jgratton72/Purple-38er/Images/Case 3D/CaseBase3D.jpg

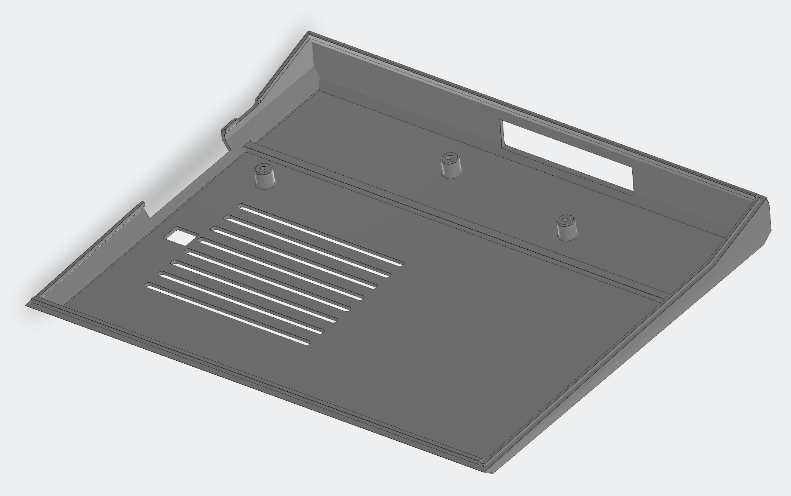
Images/Case 3D/CaseBase3D.jpg
