jgratton72/Purple-38er/Images/PCB 3D/Board3D.jpg

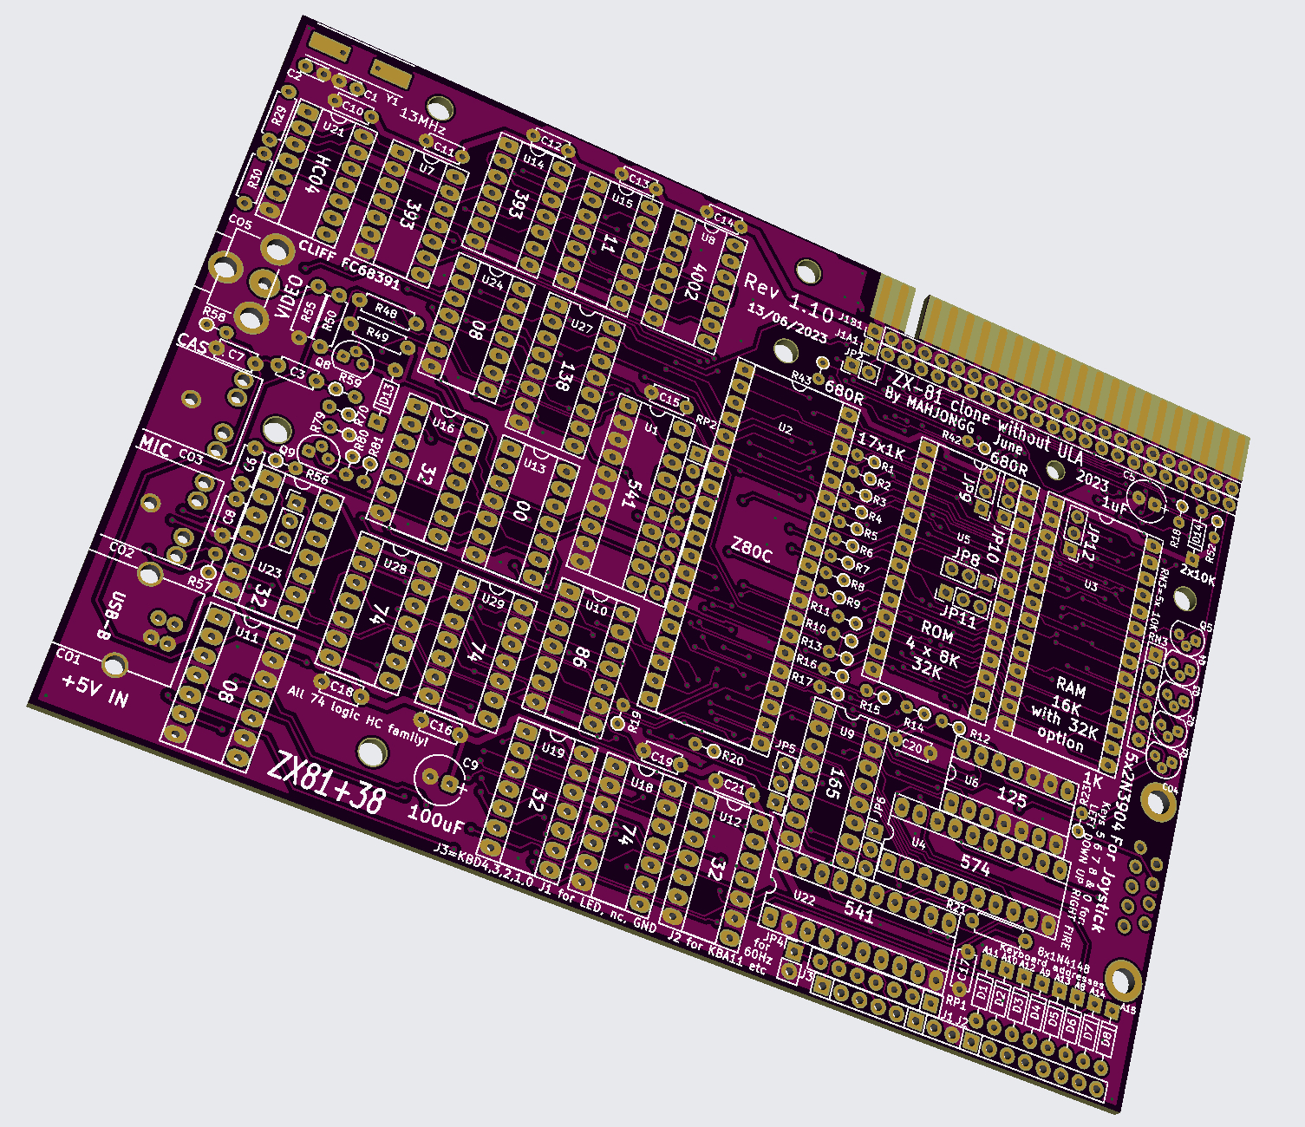
Images/PCB 3D/Board3D.jpg
