jgratton72/Purple-38er/Sources/Case/Case STEP/zx81-case-sinclair-5.step

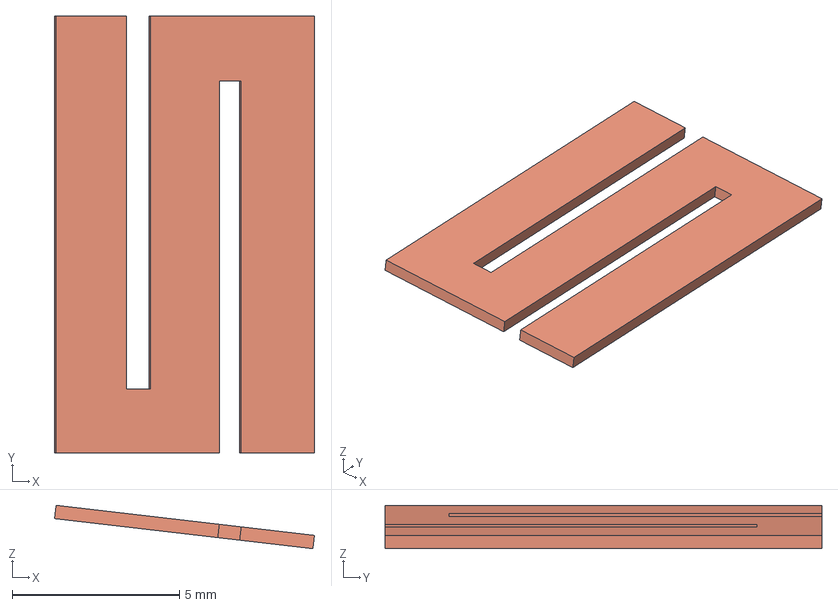
[picture p23: CAD file, 2025-08-02]
Sources/Case/Case STEP/zx81-case-sinclair-5.step
7.77 x 13.1 x 1.30 mm
