jgratton72/Purple-38er/Sources/Case/Keycap STEP/zx81-keycaps-text-b-39.step

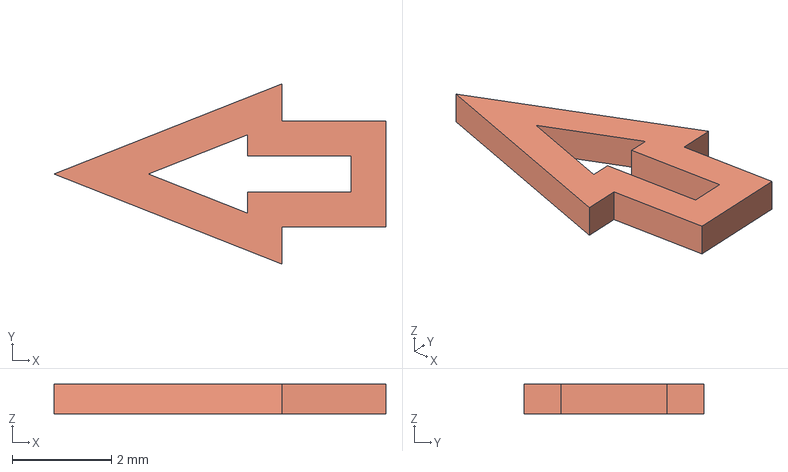
[picture p25: CAD file, 2025-08-02]
Sources/Case/Keycap STEP/zx81-keycaps-text-b-39.step
6.69 x 3.63 x 0.6 mm
