jgratton72/Purple-38er/Sources/Case/Case STEP/zx81-case-sinclair-1.step

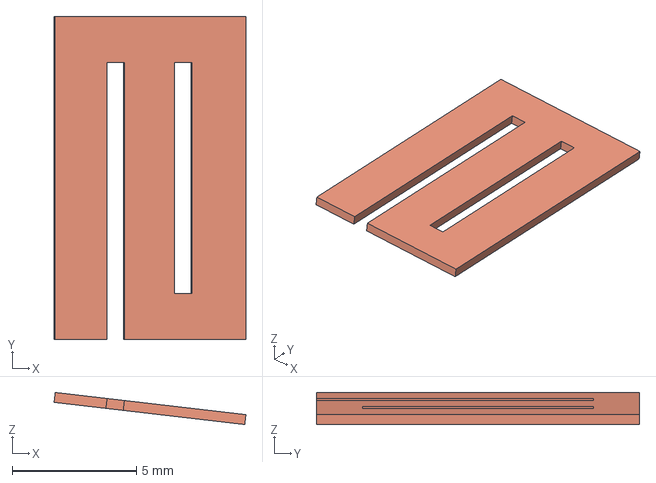
[picture p26: CAD file, 2025-08-02]
Sources/Case/Case STEP/zx81-case-sinclair-1.step
7.73 x 13.0 x 1.29 mm
