jgratton72/Purple-38er/Sources/Case/Keycap STEP/zx81-keycaps-text-b-32.step

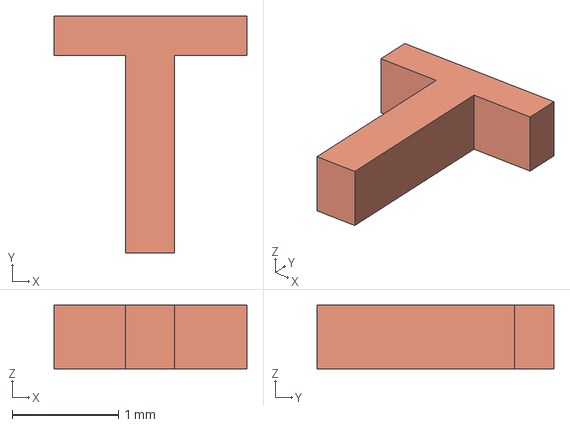
[picture p27: CAD file, 2025-08-02]
Sources/Case/Keycap STEP/zx81-keycaps-text-b-32.step
1.82 x 2.23 x 0.6 mm
