jgratton72/Purple-38er/Sources/Case/Case STEP/zx81-case-sinclair-3.step

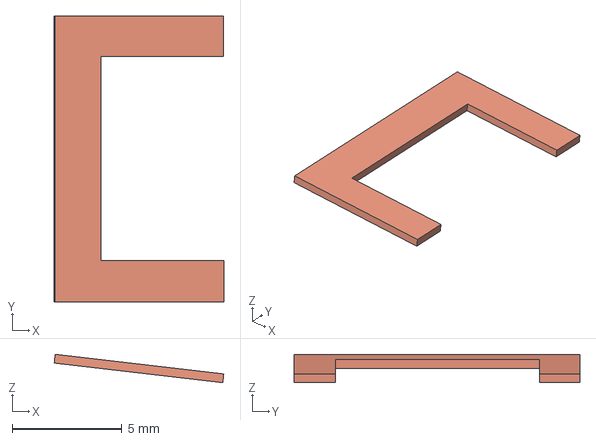
[picture p28: CAD file, 2025-08-02]
Sources/Case/Case STEP/zx81-case-sinclair-3.step
7.72 x 13.0 x 1.29 mm
