jgratton72/Purple-38er/Sources/Case/Keycap STEP/zx81-keycaps-text-b-37.step

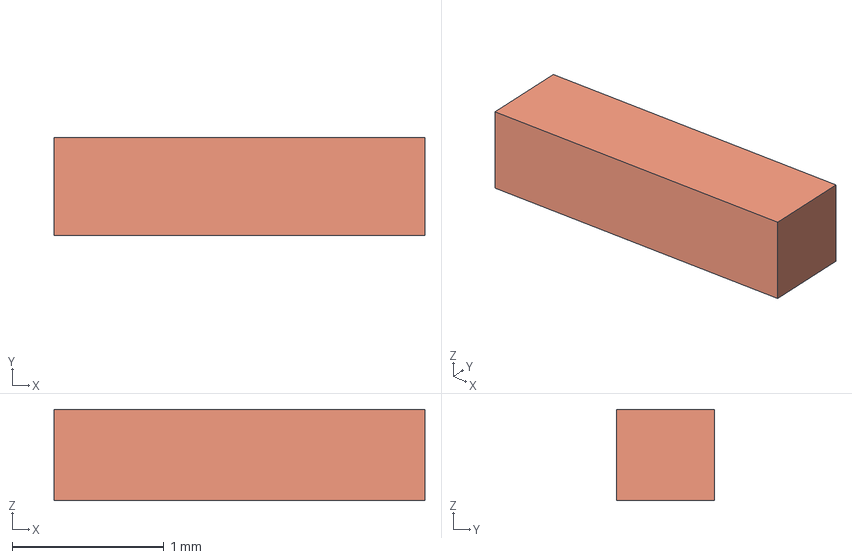
[picture p29: CAD file, 2025-08-02]
Sources/Case/Keycap STEP/zx81-keycaps-text-b-37.step
2.44 x 0.646 x 0.6 mm
