jgratton72/Purple-38er/Sources/Case/Case STEP/zx81-case-zx81-3.step

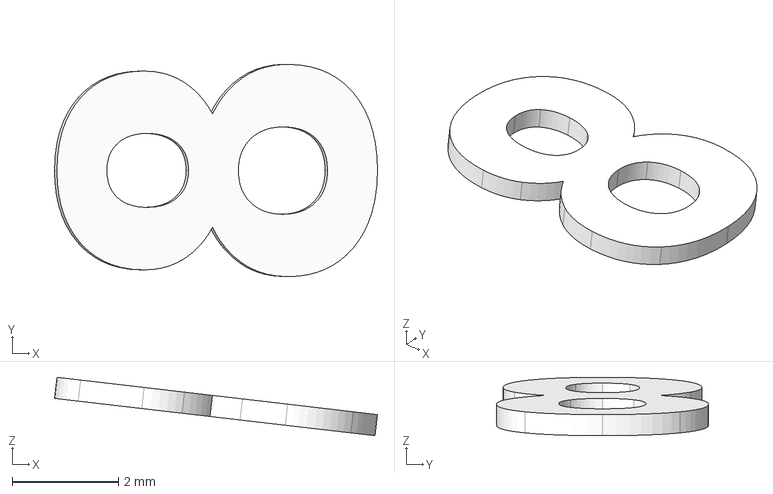
[picture p30: CAD file, 2025-08-02]
Sources/Case/Case STEP/zx81-case-zx81-3.step
6.09 x 4.00 x 1.10 mm
