jgratton72/Purple-38er/Sources/Case/Keycap STEP/zx81-keycaps-text-a-45.step

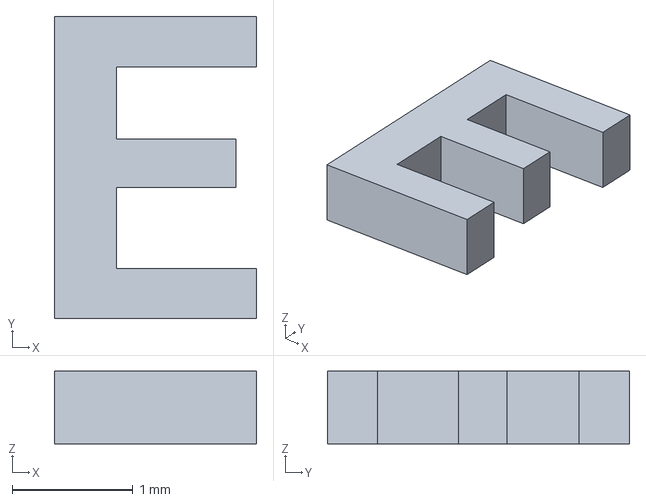
[picture p31: CAD file, 2025-08-02]
Sources/Case/Keycap STEP/zx81-keycaps-text-a-45.step
1.68 x 2.50 x 0.6 mm
