jgratton72/Purple-38er/Sources/Case/Case STEP/zx81-case-sinclair-9.step

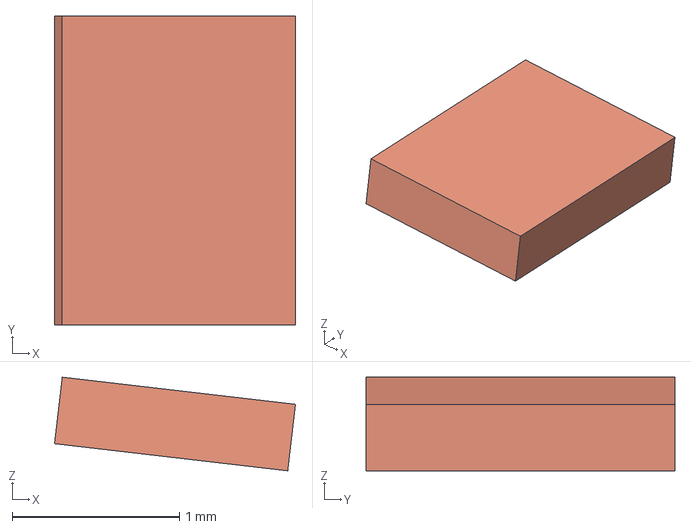
[picture p32: CAD file, 2025-08-02]
Sources/Case/Case STEP/zx81-case-sinclair-9.step
1.44 x 1.85 x 0.56 mm
