jgratton72/Purple-38er/Sources/Case/Case STEP/zx81-case-usb-mount.step

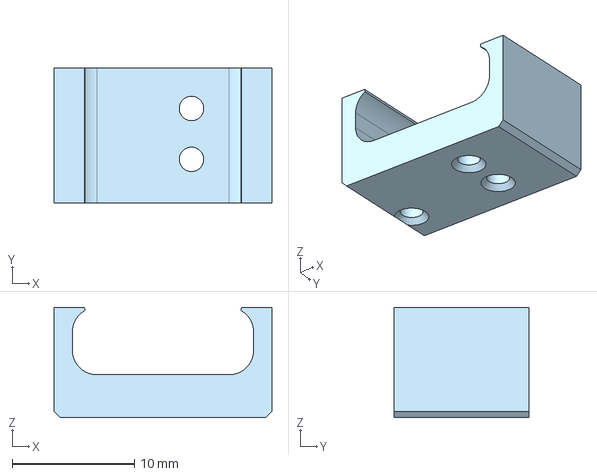
[picture p34: CAD file, 2025-08-02]
Sources/Case/Case STEP/zx81-case-usb-mount.step
17.8 x 11.0 x 9.00 mm
