jgratton72/Purple-38er/Sources/Case/Keycap STEP/zx81-keycaps-text-b-52.step

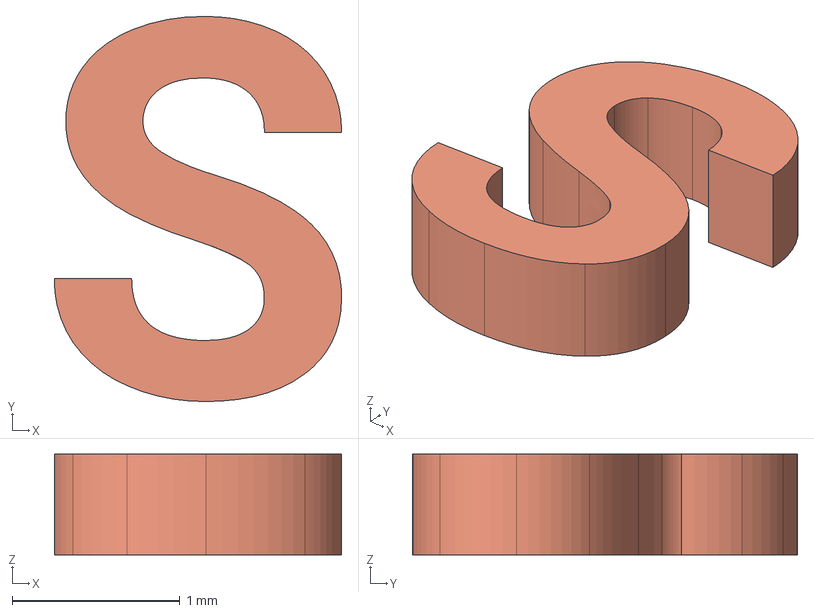
[picture p35: CAD file, 2025-08-02]
Sources/Case/Keycap STEP/zx81-keycaps-text-b-52.step
1.71 x 2.30 x 0.6 mm
