jgratton72/Purple-38er/Sources/Case/Case STEP/zx81-case-port-cover.step

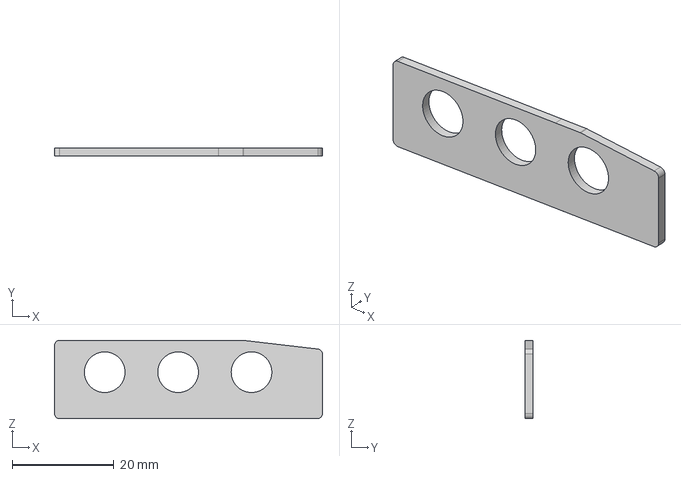
[picture p36: CAD file, 2025-08-02]
Sources/Case/Case STEP/zx81-case-port-cover.step
52.8 x 1.60 x 15.4 mm
