jgratton72/Purple-38er/Sources/Case/Keycap STEP/zx81-keycaps-text-a-16.step

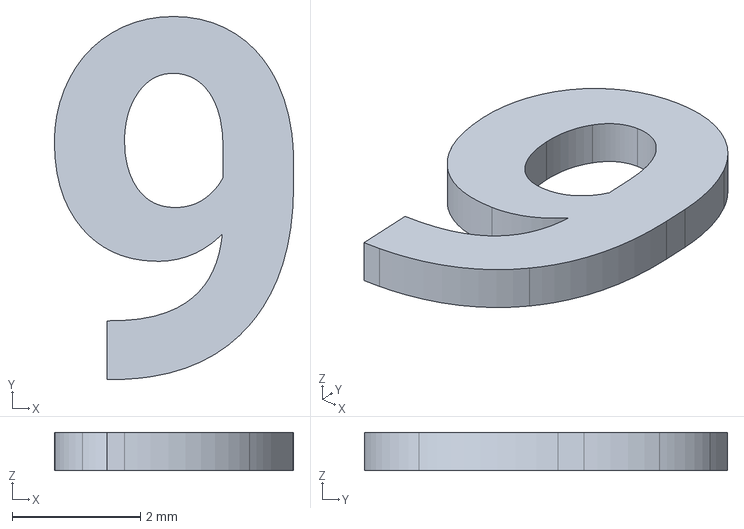
[picture p37: CAD file, 2025-08-02]
Sources/Case/Keycap STEP/zx81-keycaps-text-a-16.step
3.73 x 5.66 x 0.6 mm
