jgratton72/Purple-38er/Sources/Case/Case STEP/zx81-case-zx81-1.step

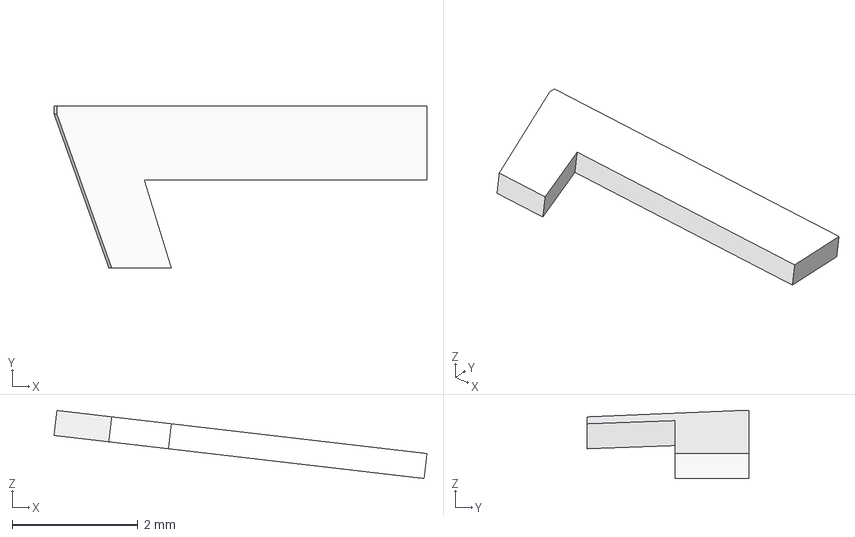
[picture p38: CAD file, 2025-08-02]
Sources/Case/Case STEP/zx81-case-zx81-1.step
5.94 x 2.58 x 1.08 mm
