jgratton72/Purple-38er/Sources/Case/Case STEP/zx81-case-zx81.step

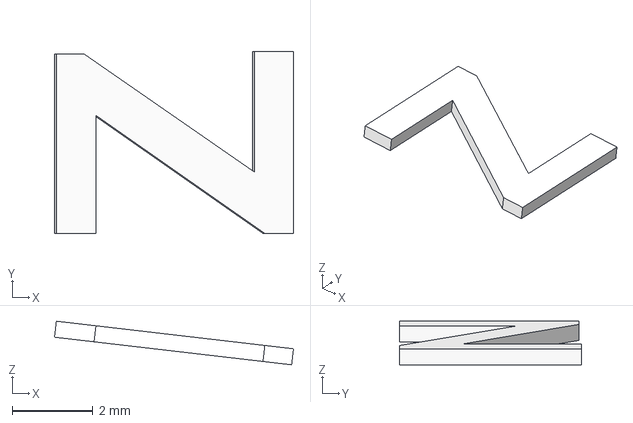
[picture p39: CAD file, 2025-08-02]
Sources/Case/Case STEP/zx81-case-zx81.step
5.93 x 4.51 x 1.08 mm
