jgratton72/Purple-38er/Sources/Case/Case STEP/zx81-case-sinclair-6.step

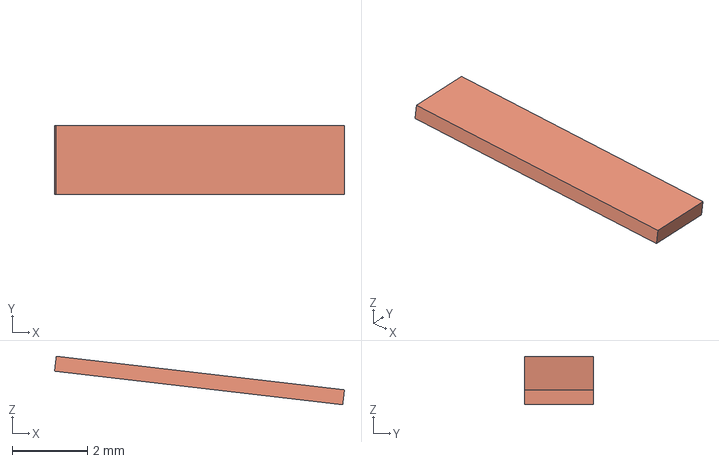
[picture p41: CAD file, 2025-08-02]
Sources/Case/Case STEP/zx81-case-sinclair-6.step
7.72 x 1.83 x 1.29 mm
