jgratton72/Purple-38er/Sources/Case/Keycap STEP/zx81-keycaps-text-a-33.step

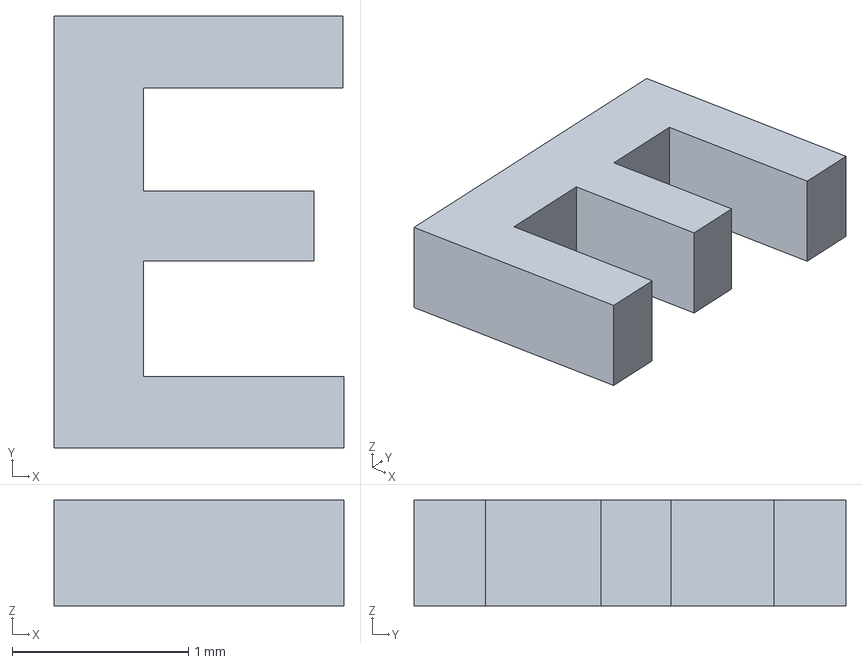
[picture p42: CAD file, 2025-08-02]
Sources/Case/Keycap STEP/zx81-keycaps-text-a-33.step
1.64 x 2.45 x 0.6 mm
