jgratton72/Purple-38er/Sources/Case/Case STEP/zx81-case-sinclair-4.step

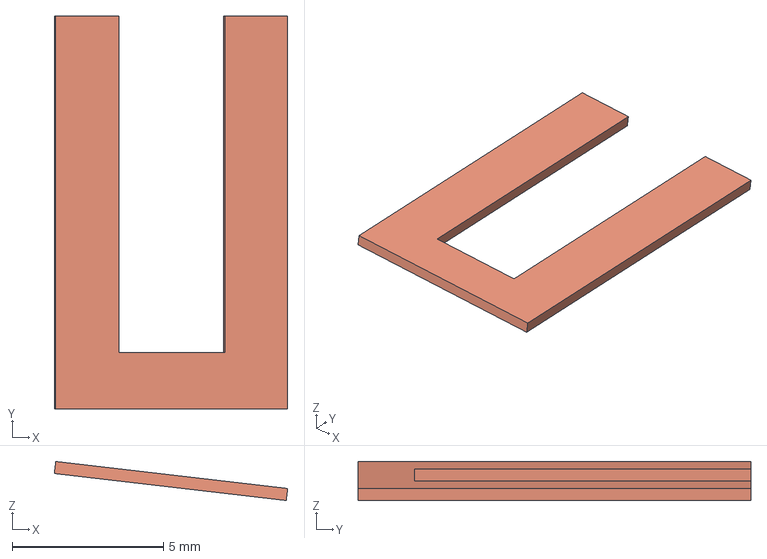
[picture p43: CAD file, 2025-08-02]
Sources/Case/Case STEP/zx81-case-sinclair-4.step
7.71 x 13.0 x 1.29 mm
