jgratton72/Purple-38er/Sources/Case/Keycap STEP/zx81-keycaps-text-b-31.step

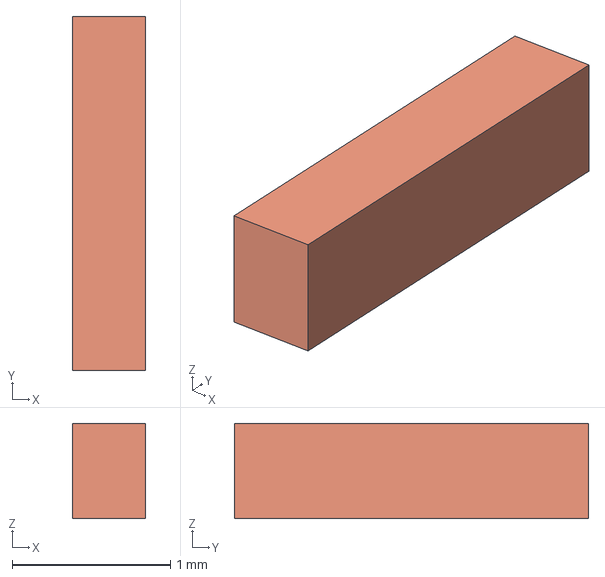
[picture p44: CAD file, 2025-08-02]
Sources/Case/Keycap STEP/zx81-keycaps-text-b-31.step
0.46 x 2.23 x 0.6 mm
