jgratton72/Purple-38er/Sources/Case/Keycap STEP/zx81-keycaps-text-a-2.step

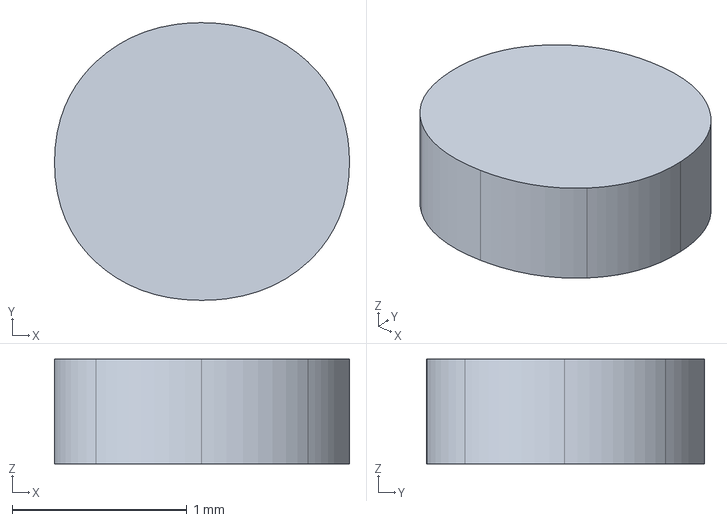
[picture p47: CAD file, 2025-08-02]
Sources/Case/Keycap STEP/zx81-keycaps-text-a-2.step
1.69 x 1.59 x 0.6 mm
