jgratton72/Purple-38er/Sources/Case/Keycap STEP/zx81-keycaps-text-b-94.step

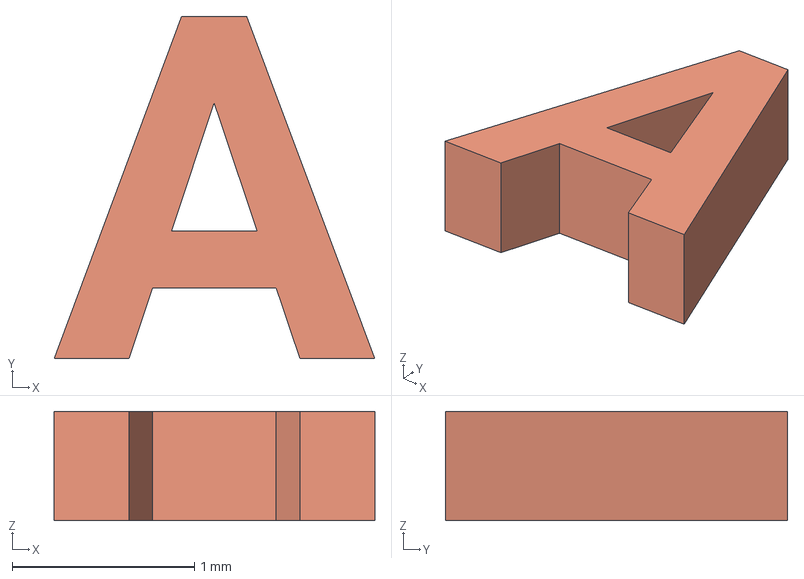
[picture p49: CAD file, 2025-08-02]
Sources/Case/Keycap STEP/zx81-keycaps-text-b-94.step
1.76 x 1.88 x 0.6 mm
