jgratton72/Purple-38er/Sources/Case/Keycap STEP/zx81-keycaps-text-b-11.step

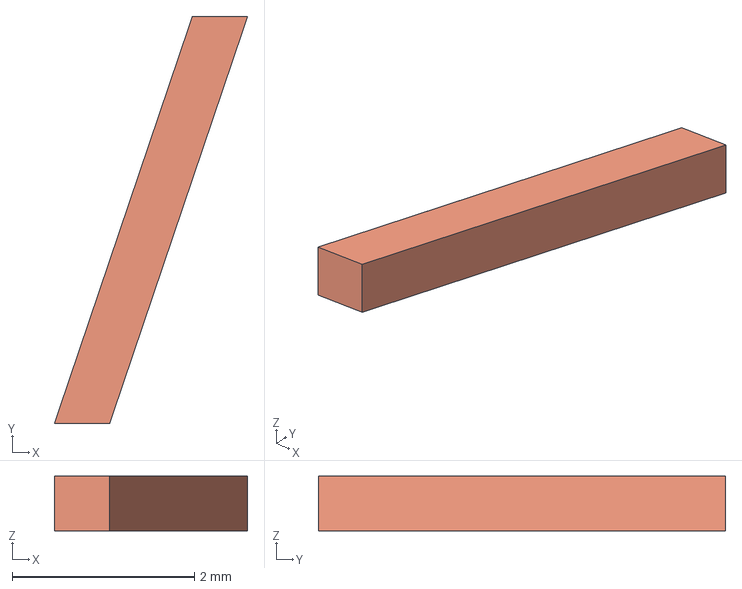
[picture p50: CAD file, 2025-08-02]
Sources/Case/Keycap STEP/zx81-keycaps-text-b-11.step
2.12 x 4.47 x 0.6 mm
