jgratton72/Purple-38er/Sources/Case/Keycap STEP/zx81-keycaps-text-b-70.step

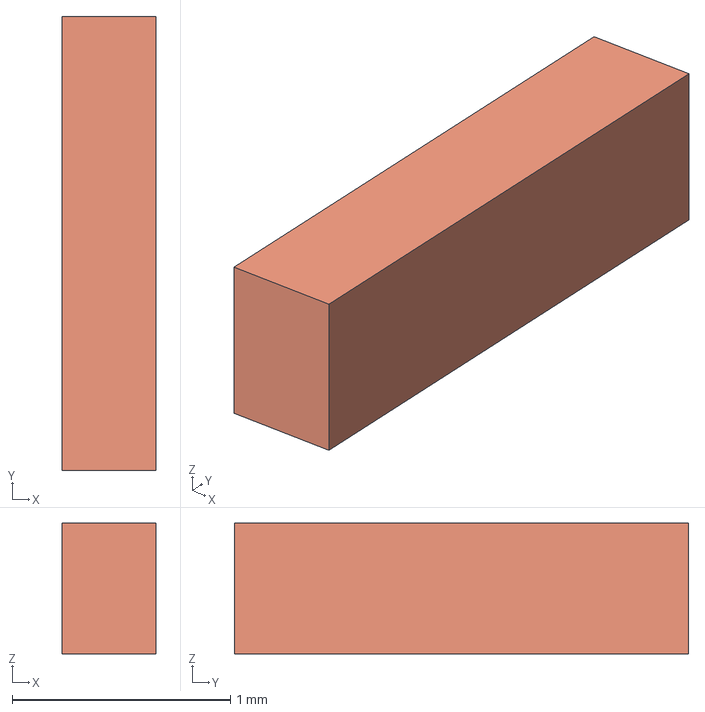
[picture p51: CAD file, 2025-08-02]
Sources/Case/Keycap STEP/zx81-keycaps-text-b-70.step
0.428 x 2.08 x 0.6 mm
