jgratton72/Purple-38er/Sources/Case/Keycap STEP/zx81-keycaps-text-b-46.step

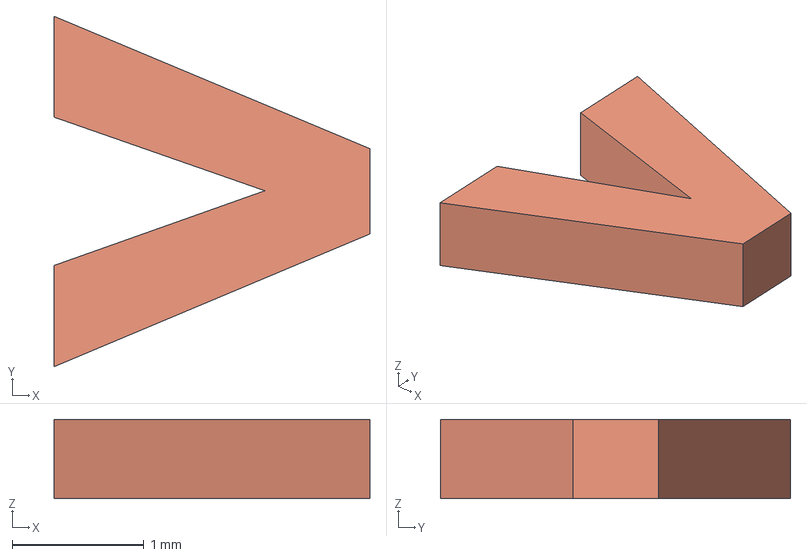
[picture p52: CAD file, 2025-08-02]
Sources/Case/Keycap STEP/zx81-keycaps-text-b-46.step
2.40 x 2.66 x 0.6 mm
