jgratton72/Purple-38er/Sources/Case/Keycap STEP/zx81-keycaps-text-b-50.step

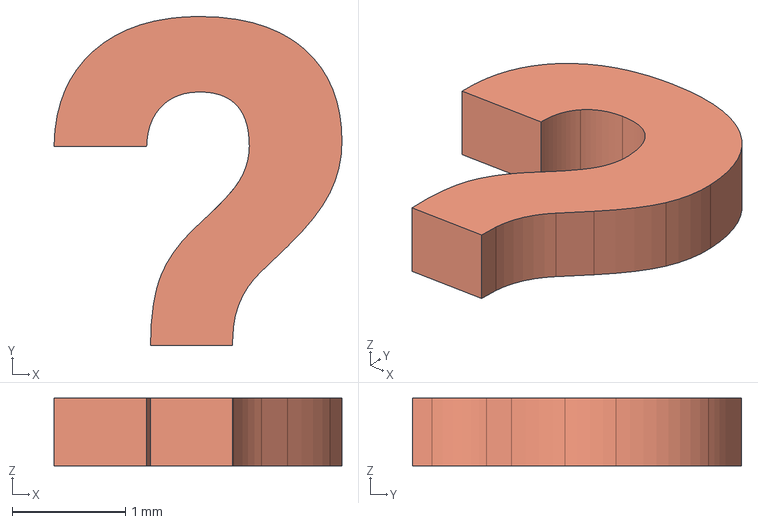
[picture p53: CAD file, 2025-08-02]
Sources/Case/Keycap STEP/zx81-keycaps-text-b-50.step
2.55 x 2.91 x 0.6 mm
