jgratton72/Purple-38er/Sources/Case/Keycap STEP/zx81-keycaps-text-b-92.step

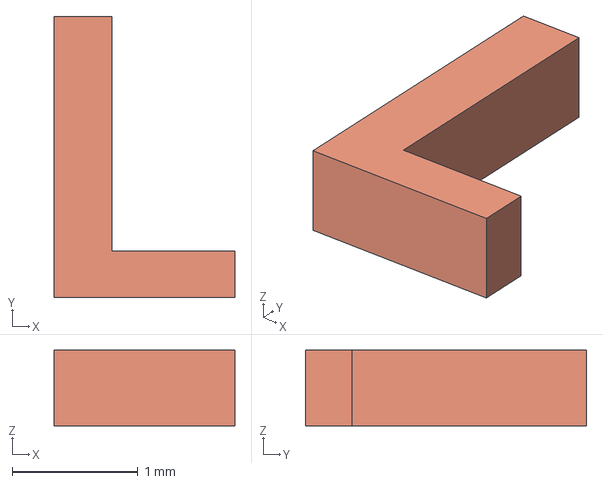
[picture p54: CAD file, 2025-08-02]
Sources/Case/Keycap STEP/zx81-keycaps-text-b-92.step
1.44 x 2.23 x 0.6 mm
