jgratton72/Purple-38er/Sources/Case/Keycap STEP/zx81-keycaps-dark-1.step

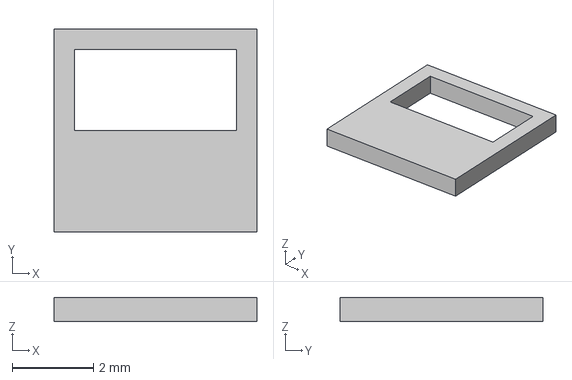
[picture p55: CAD file, 2025-08-02]
Sources/Case/Keycap STEP/zx81-keycaps-dark-1.step
5.00 x 5.00 x 0.6 mm
