jgratton72/Purple-38er/Sources/Case/Keycap STEP/zx81-keycaps-light-4.step

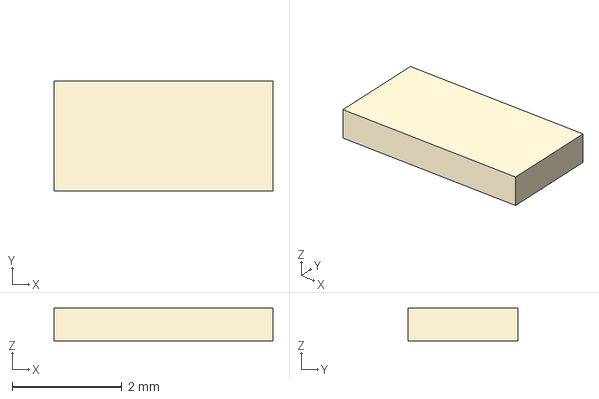
[picture p56: CAD file, 2025-08-02]
Sources/Case/Keycap STEP/zx81-keycaps-light-4.step
4.00 x 2.00 x 0.6 mm
