jgratton72/Purple-38er/Sources/Case/Keycap STEP/zx81-keycaps-text-a-37.step

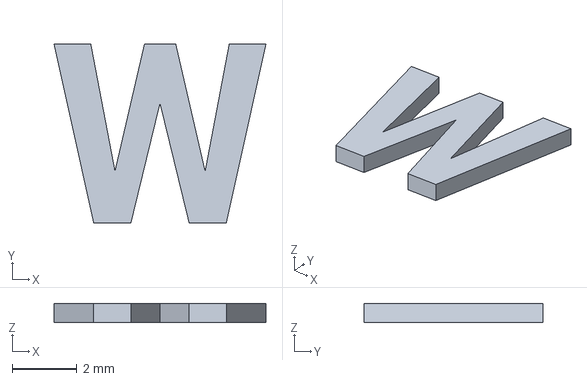
[picture p58: CAD file, 2025-08-02]
Sources/Case/Keycap STEP/zx81-keycaps-text-a-37.step
6.55 x 5.53 x 0.6 mm
