jgratton72/Purple-38er/Sources/Case/Keycap STEP/zx81-keycaps-text-a-38.step

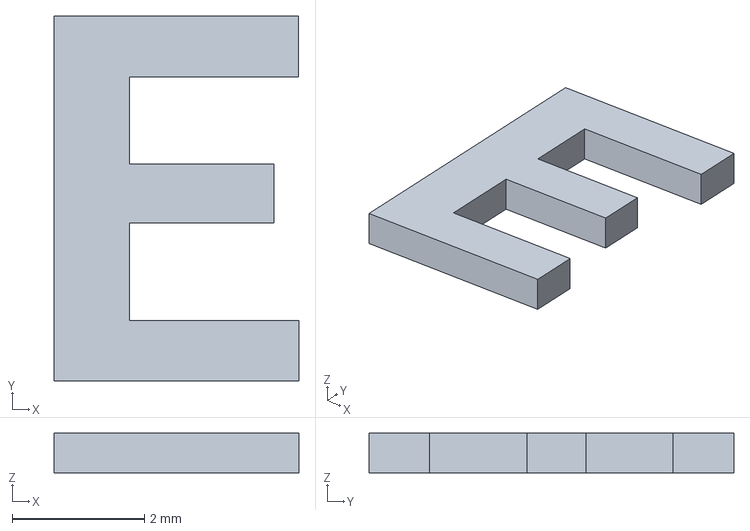
[picture p59: CAD file, 2025-08-02]
Sources/Case/Keycap STEP/zx81-keycaps-text-a-38.step
3.71 x 5.53 x 0.6 mm
