jgratton72/Purple-38er/Sources/Case/Keycap STEP/zx81-keycaps-text-b-72.step

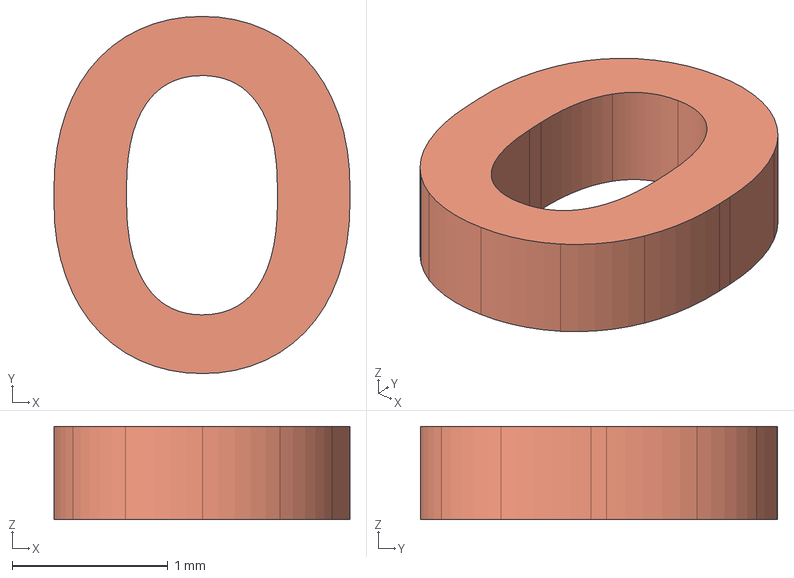
[picture p60: CAD file, 2025-08-02]
Sources/Case/Keycap STEP/zx81-keycaps-text-b-72.step
1.90 x 2.29 x 0.6 mm
