jgratton72/Purple-38er/Sources/Case/Keycap STEP/zx81-keycaps-text-a-14.step

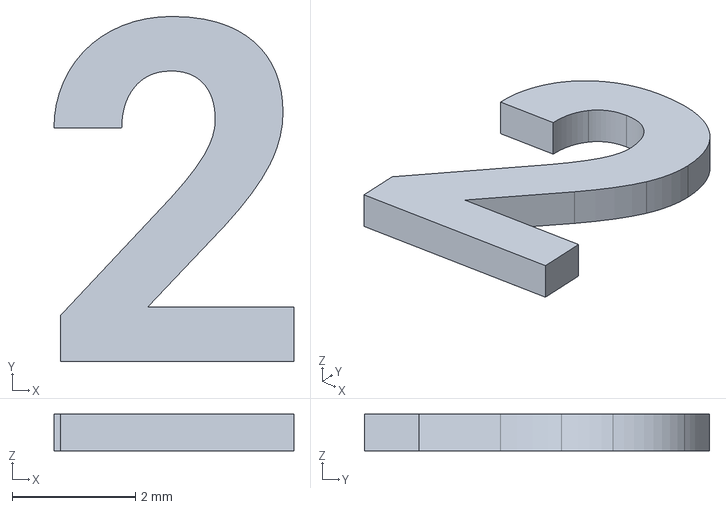
[picture p61: CAD file, 2025-08-02]
Sources/Case/Keycap STEP/zx81-keycaps-text-a-14.step
3.90 x 5.61 x 0.6 mm
