jgratton72/Purple-38er/Sources/Case/Keycap STEP/zx81-keycaps-text-a-27.step

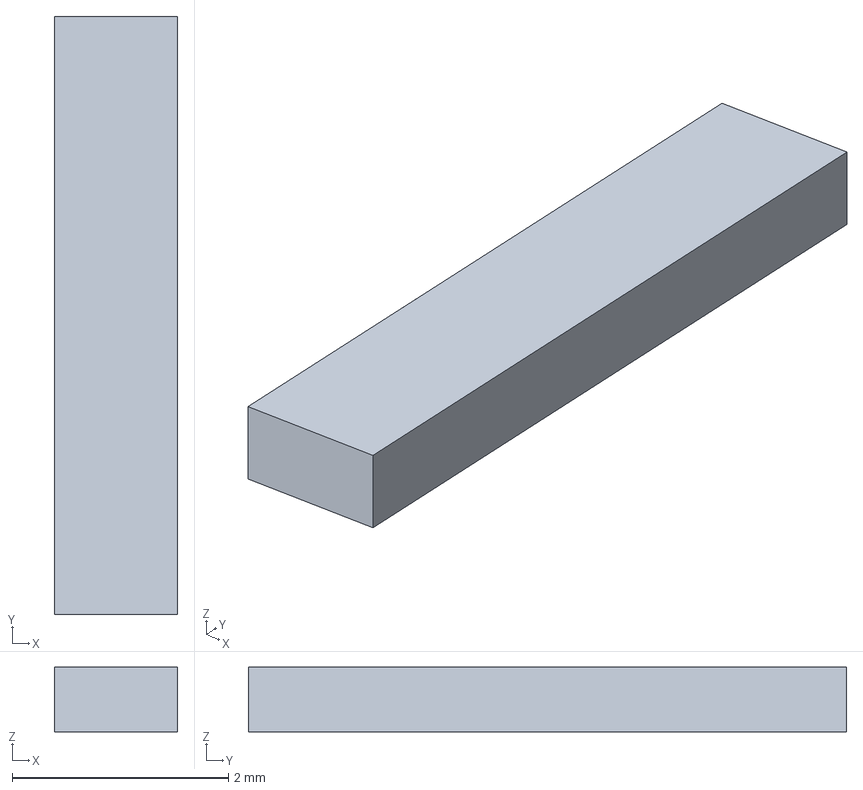
[picture p62: CAD file, 2025-08-02]
Sources/Case/Keycap STEP/zx81-keycaps-text-a-27.step
1.14 x 5.53 x 0.6 mm
