jgratton72/Purple-38er/Sources/Case/Keycap STEP/zx81-keycaps-white-8.step

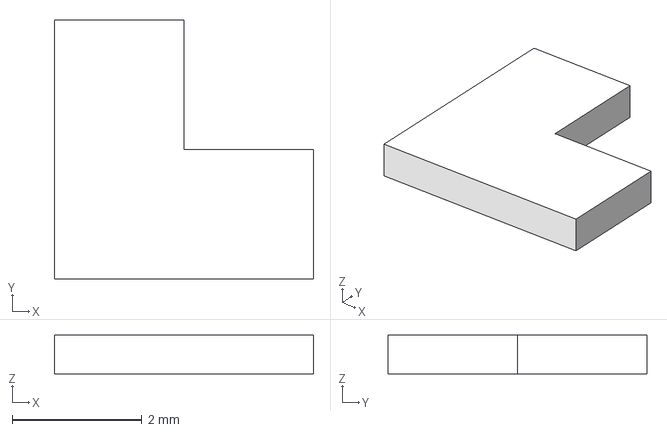
[picture p63: CAD file, 2025-08-02]
Sources/Case/Keycap STEP/zx81-keycaps-white-8.step
4.00 x 4.00 x 0.6 mm
