jgratton72/Purple-38er/Sources/Case/Keycap STEP/zx81-keycaps-text-a-23.step

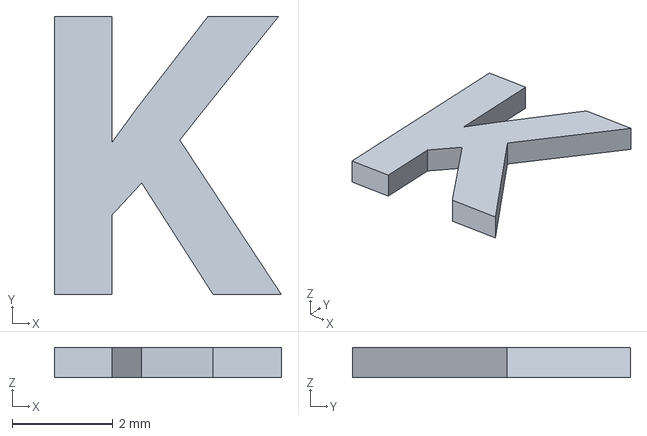
[picture p65: CAD file, 2025-08-02]
Sources/Case/Keycap STEP/zx81-keycaps-text-a-23.step
4.51 x 5.53 x 0.6 mm
