jgratton72/Purple-38er/Sources/Case/Keycap STEP/zx81-keycaps-text-b-65.step

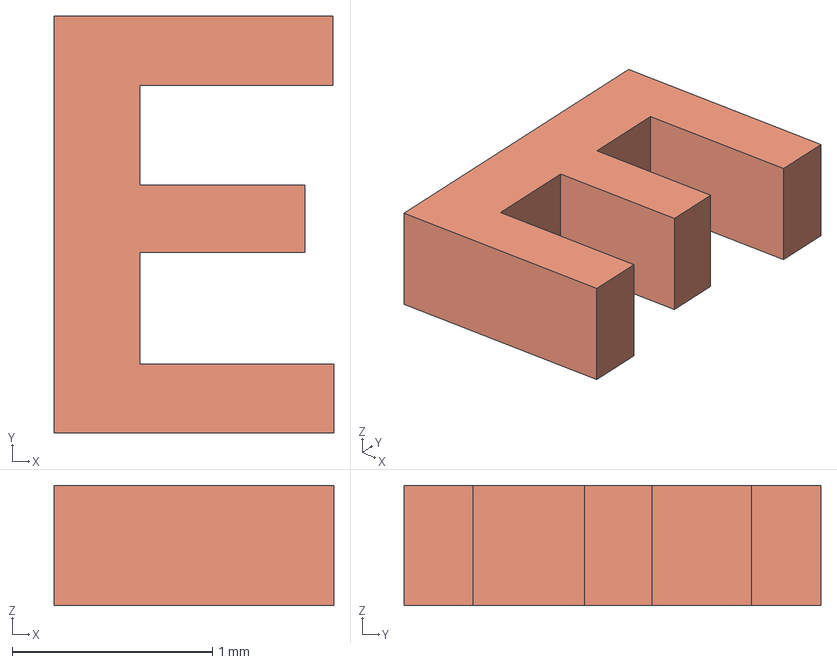
[picture p66: CAD file, 2025-08-02]
Sources/Case/Keycap STEP/zx81-keycaps-text-b-65.step
1.39 x 2.08 x 0.6 mm
