jgratton72/Purple-38er/Sources/Case/Keycap STEP/zx81-keycaps-text-b-104.step

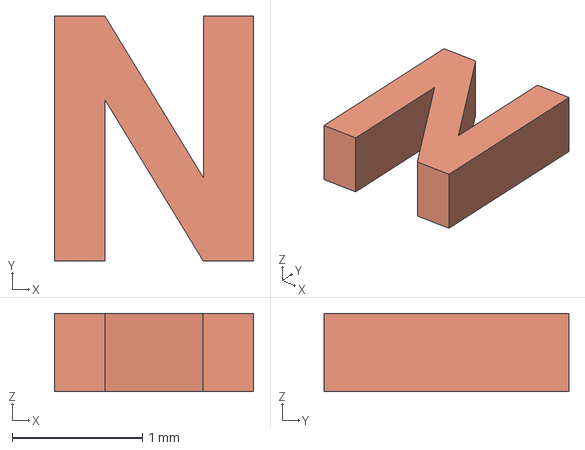
[picture p67: CAD file, 2025-08-02]
Sources/Case/Keycap STEP/zx81-keycaps-text-b-104.step
1.53 x 1.88 x 0.6 mm
