jgratton72/Purple-38er/Sources/Case/Keycap STEP/zx81-keycaps-text-a-43.step

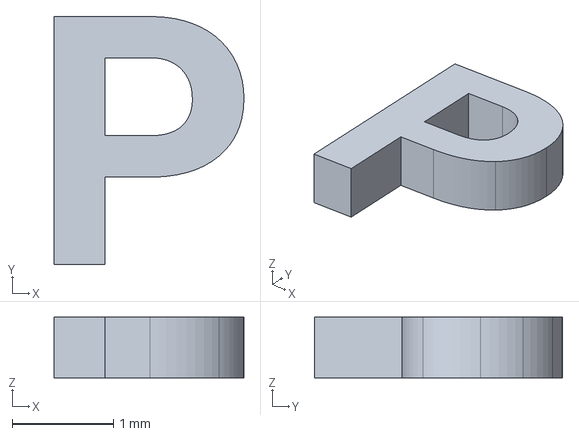
[picture p68: CAD file, 2025-08-02]
Sources/Case/Keycap STEP/zx81-keycaps-text-a-43.step
1.88 x 2.45 x 0.6 mm
