jgratton72/Purple-38er/Sources/Case/Keycap STEP/zx81-keycaps-text-a-10.step

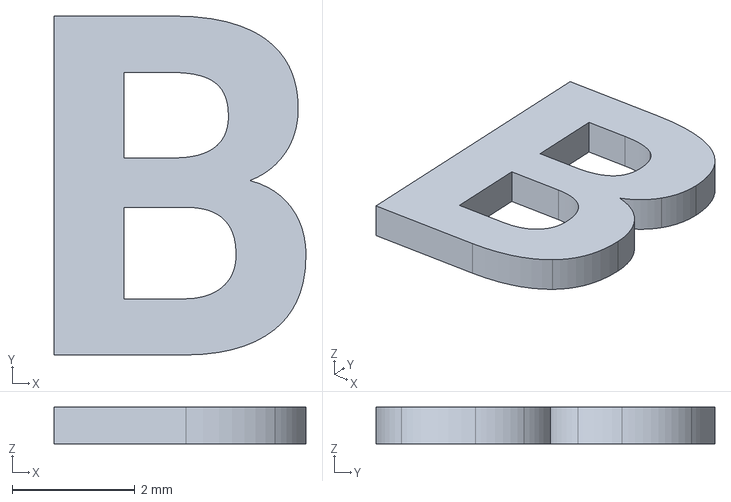
[picture p69: CAD file, 2025-08-02]
Sources/Case/Keycap STEP/zx81-keycaps-text-a-10.step
4.11 x 5.53 x 0.6 mm
