jgratton72/Purple-38er/Sources/Case/Keycap STEP/zx81-keycaps-text-a-6.step

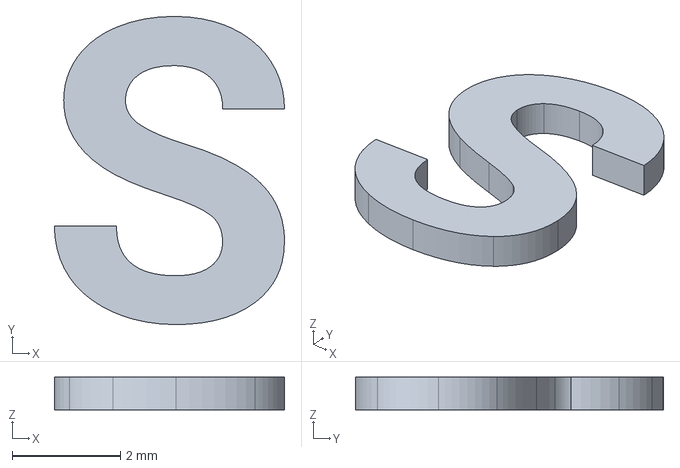
[picture p70: CAD file, 2025-08-02]
Sources/Case/Keycap STEP/zx81-keycaps-text-a-6.step
4.24 x 5.68 x 0.6 mm
