jgratton72/Purple-38er/Sources/Case/Keycap STEP/zx81-keycaps-text-b-81.step

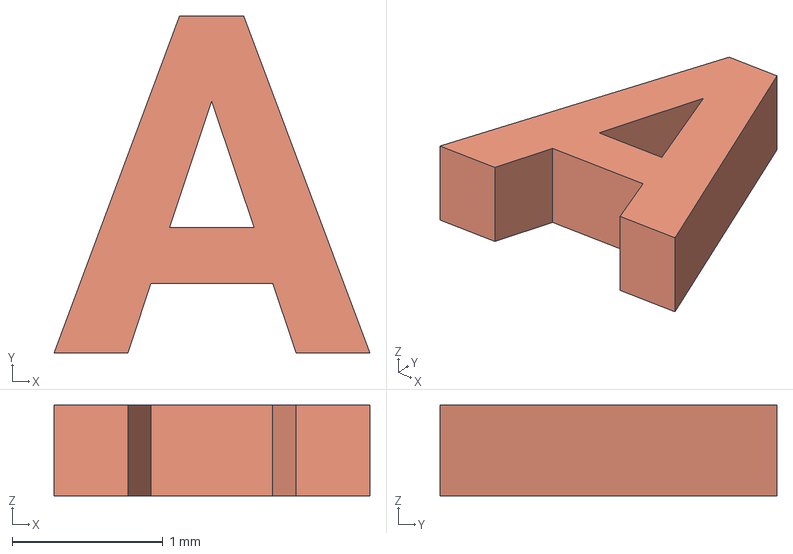
[picture p71: CAD file, 2025-08-02]
Sources/Case/Keycap STEP/zx81-keycaps-text-b-81.step
2.09 x 2.23 x 0.6 mm
