jgratton72/Purple-38er/Sources/Case/Keycap STEP/zx81-keycaps-text-a-36.step

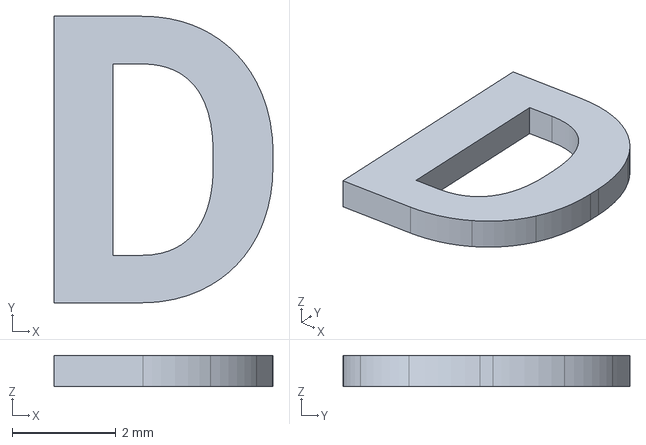
[picture p72: CAD file, 2025-08-02]
Sources/Case/Keycap STEP/zx81-keycaps-text-a-36.step
4.23 x 5.53 x 0.6 mm
