jgratton72/Purple-38er/Sources/Case/Keycap STEP/zx81-keycaps-text-b-18.step

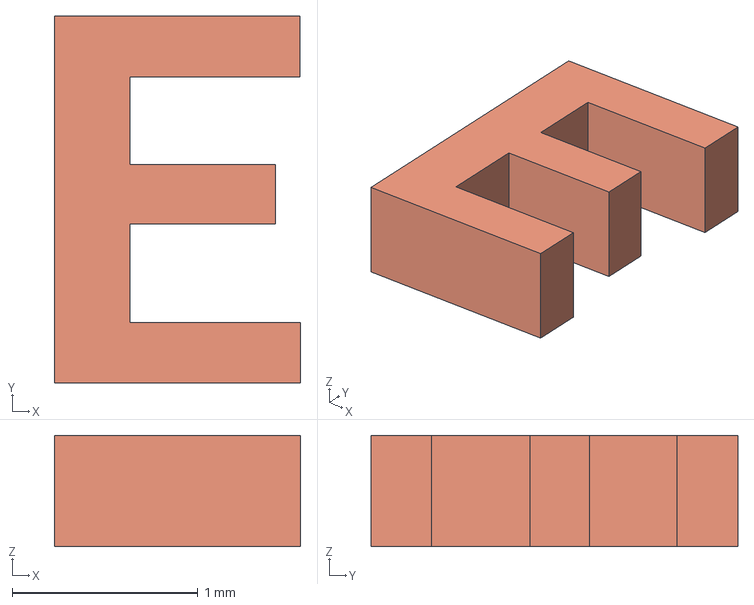
[picture p73: CAD file, 2025-08-02]
Sources/Case/Keycap STEP/zx81-keycaps-text-b-18.step
1.32 x 1.97 x 0.6 mm
