jgratton72/Purple-38er/Sources/Case/Keycap STEP/zx81-keycaps-text-b-61.step

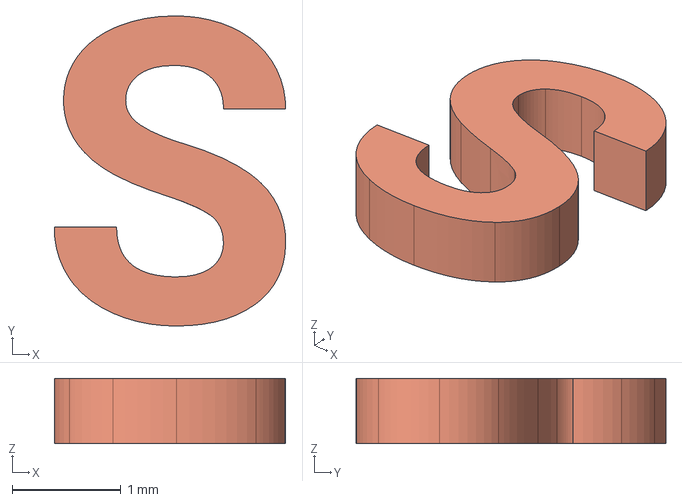
[picture p74: CAD file, 2025-08-02]
Sources/Case/Keycap STEP/zx81-keycaps-text-b-61.step
2.13 x 2.85 x 0.6 mm
