jgratton72/Purple-38er/Sources/Case/Keycap STEP/zx81-keycaps-text-a-18.step

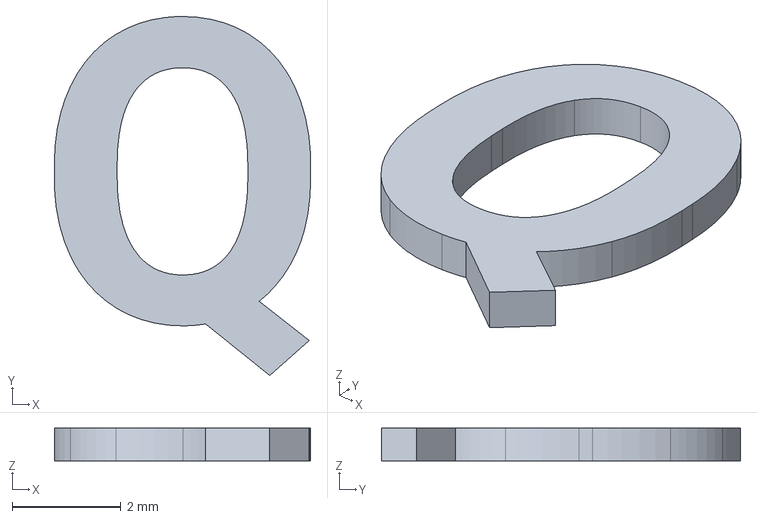
[picture p75: CAD file, 2025-08-02]
Sources/Case/Keycap STEP/zx81-keycaps-text-a-18.step
4.71 x 6.59 x 0.6 mm
