jgratton72/Purple-38er/Sources/Case/Keycap STEP/zx81-keycaps-text-b-69.step

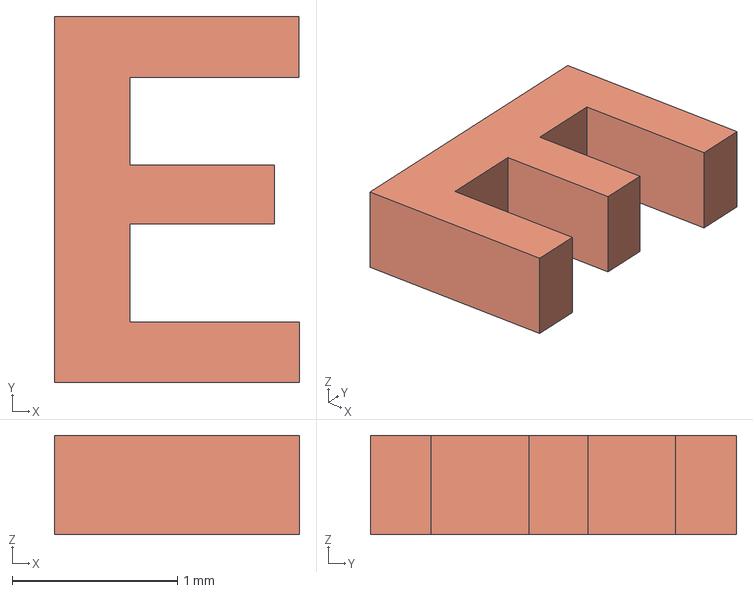
[picture p76: CAD file, 2025-08-02]
Sources/Case/Keycap STEP/zx81-keycaps-text-b-69.step
1.49 x 2.22 x 0.6 mm
