jgratton72/Purple-38er/Sources/Case/Keycap STEP/zx81-keycaps-text-a-19.step

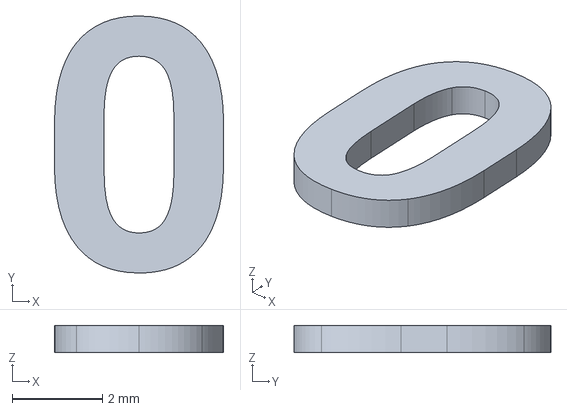
[picture p78: CAD file, 2025-08-02]
Sources/Case/Keycap STEP/zx81-keycaps-text-a-19.step
3.74 x 5.68 x 0.6 mm
