jgratton72/Purple-38er/Sources/Case/Keycap STEP/zx81-keycaps-text-b-35.step

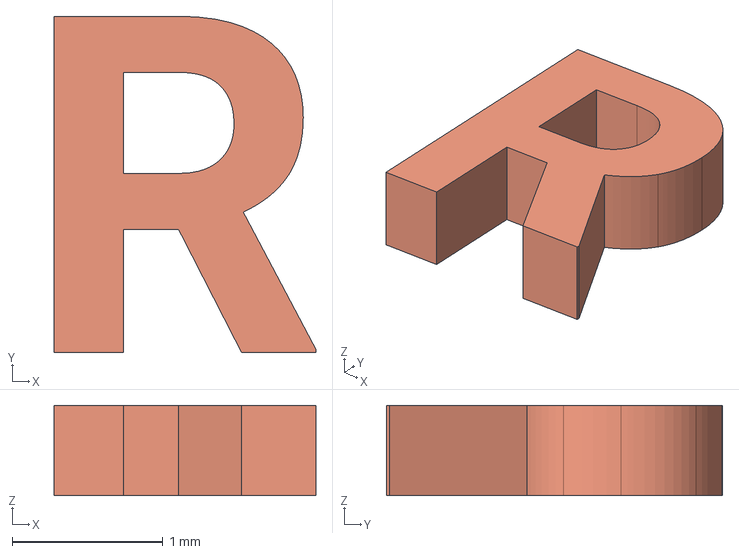
[picture p79: CAD file, 2025-08-02]
Sources/Case/Keycap STEP/zx81-keycaps-text-b-35.step
1.74 x 2.23 x 0.6 mm
