jgratton72/Purple-38er/Sources/Case/Keycap STEP/zx81-keycaps-text-b-42.step

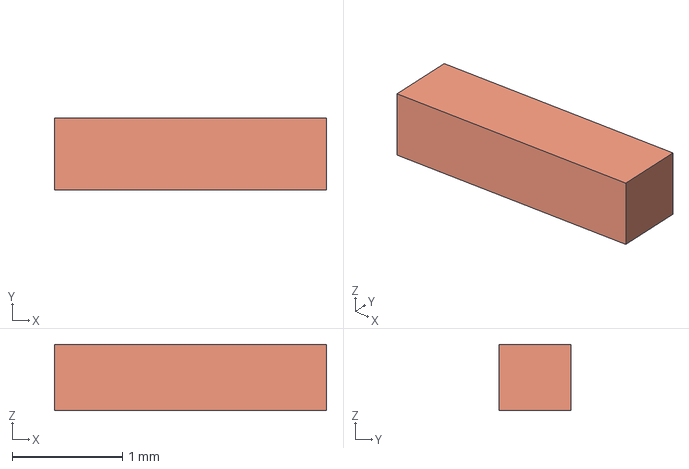
[picture p80: CAD file, 2025-08-02]
Sources/Case/Keycap STEP/zx81-keycaps-text-b-42.step
2.46 x 0.65 x 0.6 mm
