jgratton72/Purple-38er/Sources/Case/Keycap STEP/zx81-keycaps-text-b-41.step

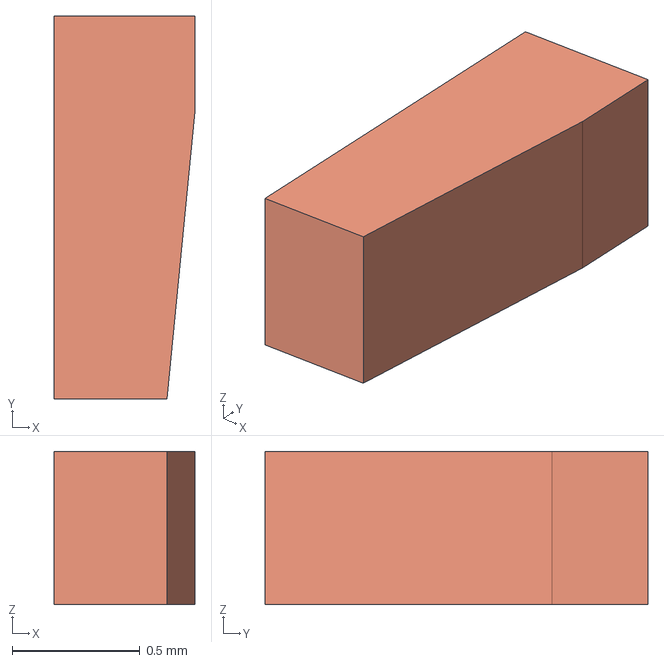
[picture p81: CAD file, 2025-08-02]
Sources/Case/Keycap STEP/zx81-keycaps-text-b-41.step
0.552 x 1.50 x 0.6 mm
