jgratton72/Purple-38er/Sources/Case/Keycap STEP/zx81-keycaps-text-b-6.step

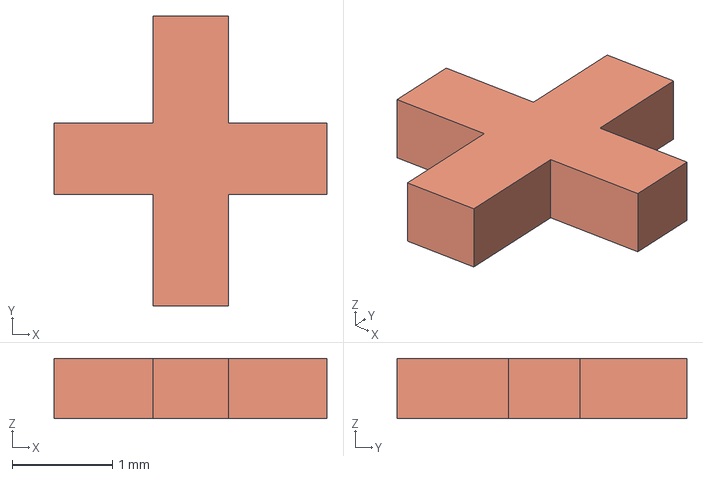
[picture p82: CAD file, 2025-08-02]
Sources/Case/Keycap STEP/zx81-keycaps-text-b-6.step
2.73 x 2.90 x 0.6 mm
