jgratton72/Purple-38er/Sources/Case/Keycap STEP/zx81-keycaps-text-a-15.step

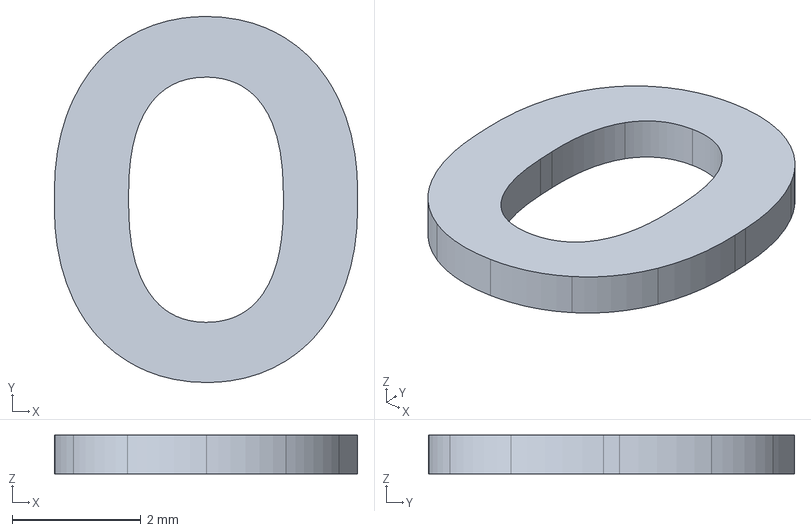
[picture p83: CAD file, 2025-08-02]
Sources/Case/Keycap STEP/zx81-keycaps-text-a-15.step
4.71 x 5.68 x 0.6 mm
