jgratton72/Purple-38er/Sources/Case/Keycap STEP/zx81-keycaps-text-a-7.step

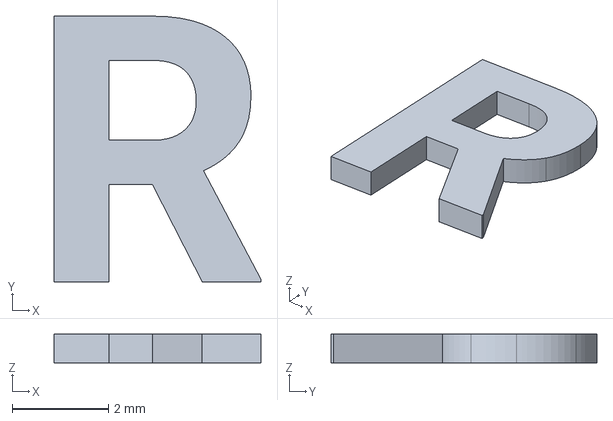
[picture p85: CAD file, 2025-08-02]
Sources/Case/Keycap STEP/zx81-keycaps-text-a-7.step
4.31 x 5.53 x 0.6 mm
