jgratton72/Purple-38er/Sources/Case/Keycap STEP/zx81-keycaps-text-b-8.step

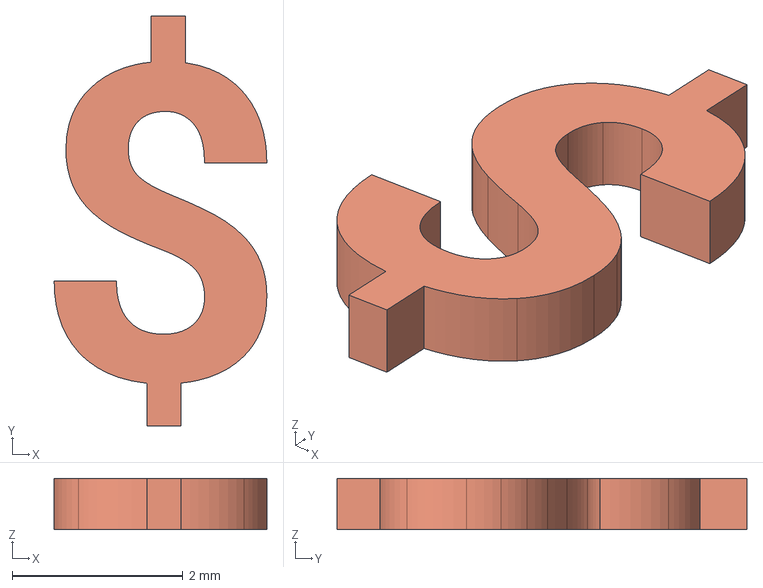
[picture p86: CAD file, 2025-08-02]
Sources/Case/Keycap STEP/zx81-keycaps-text-b-8.step
2.49 x 4.81 x 0.6 mm
