jgratton72/Purple-38er/Sources/Case/Keycap STEP/zx81-keycaps-text-a-3.step

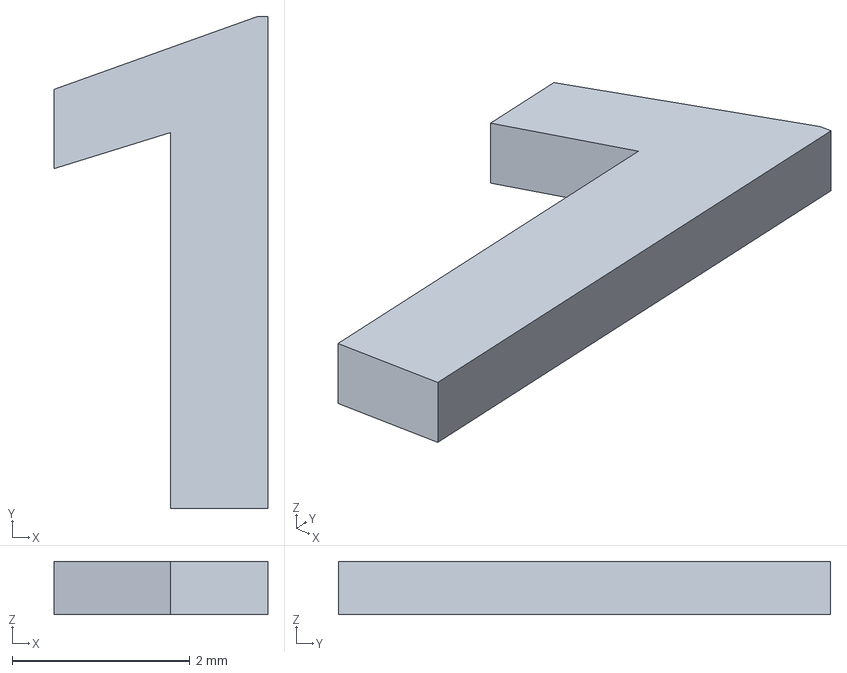
[picture p87: CAD file, 2025-08-02]
Sources/Case/Keycap STEP/zx81-keycaps-text-a-3.step
2.41 x 5.54 x 0.6 mm
