jgratton72/Purple-38er/Sources/Case/Keycap STEP/zx81-keycaps-text-a-1.step

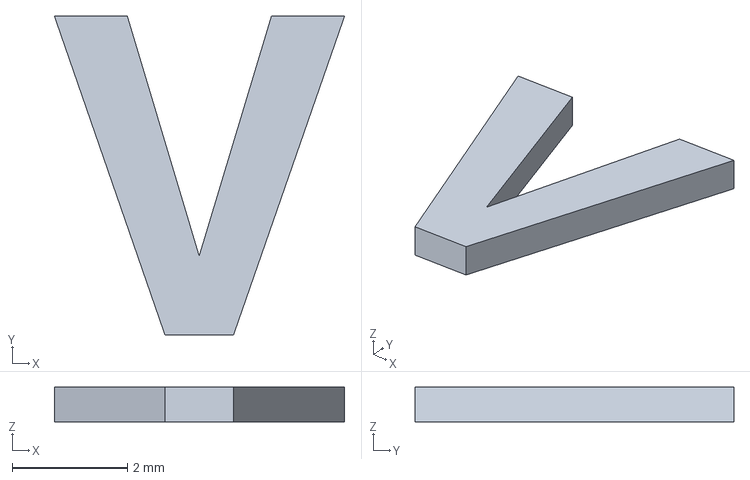
[picture p88: CAD file, 2025-08-02]
Sources/Case/Keycap STEP/zx81-keycaps-text-a-1.step
5.03 x 5.53 x 0.6 mm
