jgratton72/Purple-38er/Sources/Case/Keycap STEP/zx81-keycaps-text-b-43.step

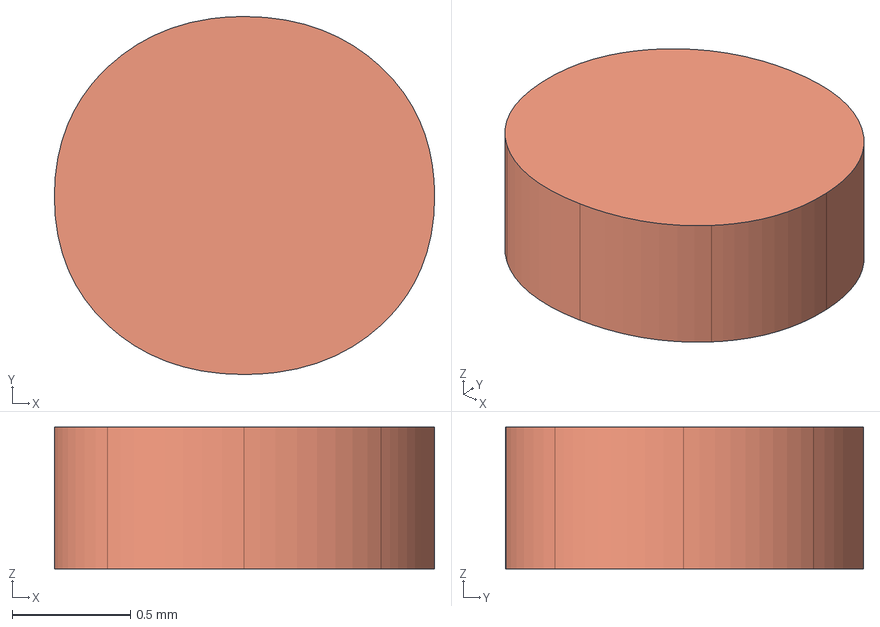
[picture p89: CAD file, 2025-08-02]
Sources/Case/Keycap STEP/zx81-keycaps-text-b-43.step
1.61 x 1.52 x 0.6 mm
