jgratton72/Purple-38er/Sources/Case/Keycap STEP/zx81-keycaps-text-b-20.step

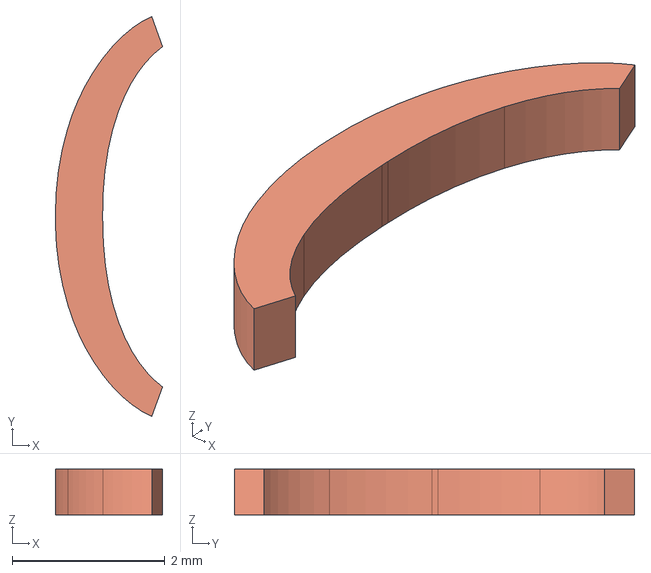
[picture p90: CAD file, 2025-08-02]
Sources/Case/Keycap STEP/zx81-keycaps-text-b-20.step
1.40 x 5.23 x 0.6 mm
