jgratton72/Purple-38er/Sources/Case/Keycap STEP/zx81-keycaps-text-b-91.step

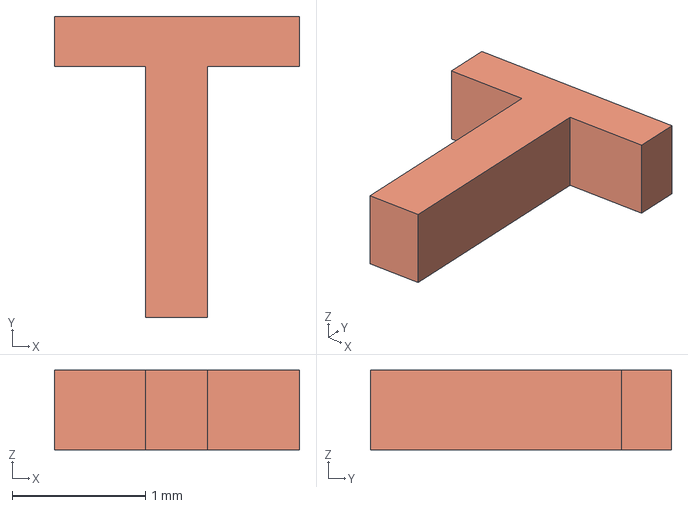
[picture p91: CAD file, 2025-08-02]
Sources/Case/Keycap STEP/zx81-keycaps-text-b-91.step
1.84 x 2.26 x 0.6 mm
