jgratton72/Purple-38er/Sources/Case/Keycap STEP/zx81-keycaps-text-b-9.step

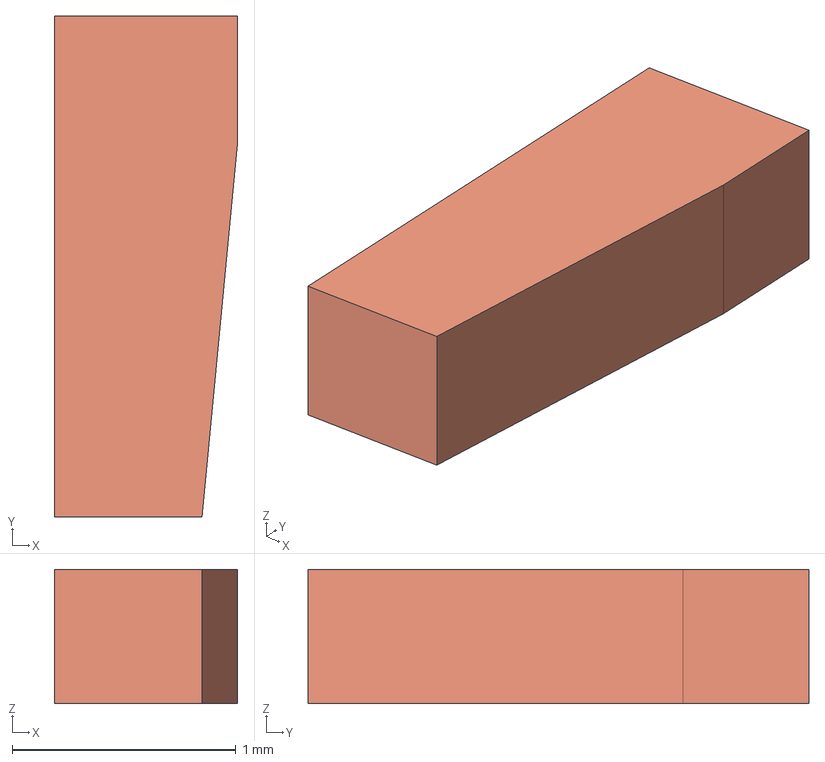
[picture p92: CAD file, 2025-08-02]
Sources/Case/Keycap STEP/zx81-keycaps-text-b-9.step
0.819 x 2.24 x 0.6 mm
