jgratton72/Purple-38er/Sources/Case/Keycap STEP/zx81-keycaps-text-b-64.step

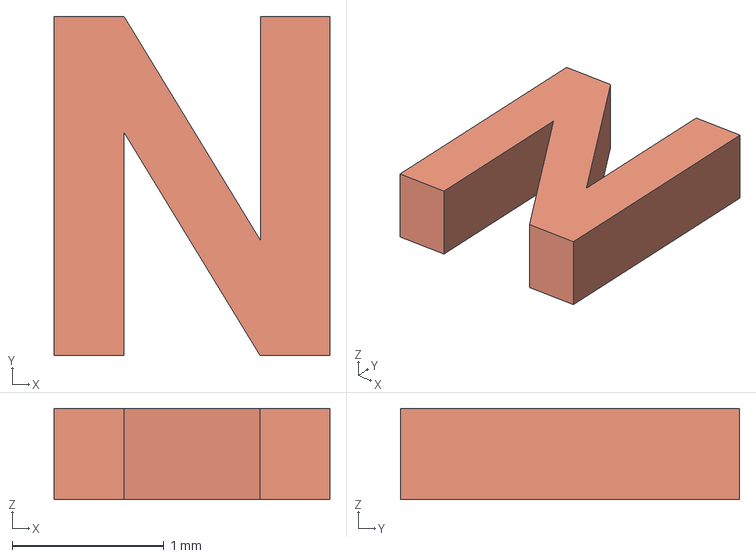
[picture p94: CAD file, 2025-08-02]
Sources/Case/Keycap STEP/zx81-keycaps-text-b-64.step
1.82 x 2.23 x 0.6 mm
