jgratton72/Purple-38er/Sources/Case/Keycap STEP/zx81-keycaps-white-5.step

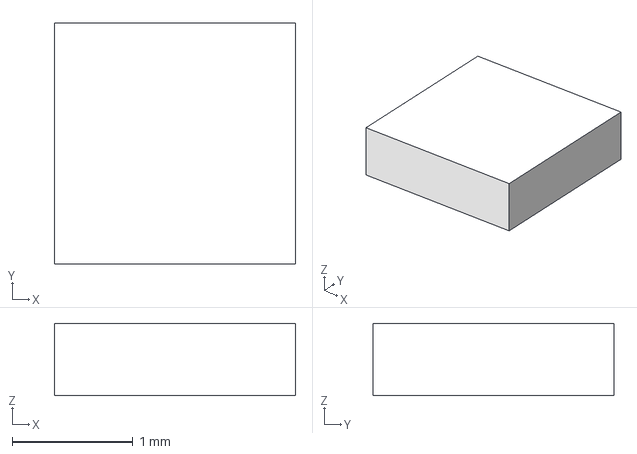
[picture p95: CAD file, 2025-08-02]
Sources/Case/Keycap STEP/zx81-keycaps-white-5.step
2.00 x 2.00 x 0.6 mm
