jgratton72/Purple-38er/Sources/Case/Keycap STEP/zx81-keycaps-text-b-21.step

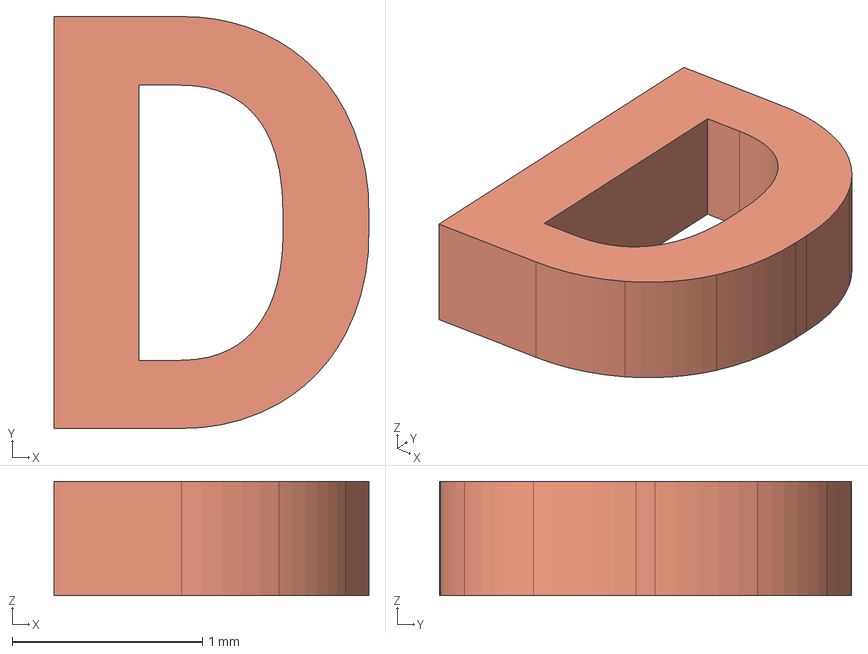
[picture p97: CAD file, 2025-08-02]
Sources/Case/Keycap STEP/zx81-keycaps-text-b-21.step
1.65 x 2.17 x 0.6 mm
