jgratton72/Purple-38er/Sources/Case/Keycap STEP/zx81-keycaps-text-b-34.step

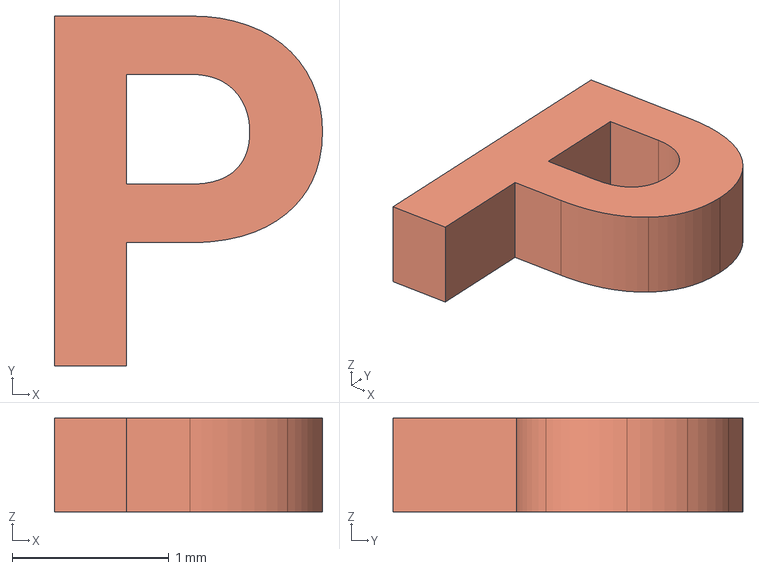
[picture p98: CAD file, 2025-08-02]
Sources/Case/Keycap STEP/zx81-keycaps-text-b-34.step
1.71 x 2.23 x 0.6 mm
