jgratton72/Purple-38er/Sources/Case/Keycap STEP/zx81-keycaps-text-b-83.step

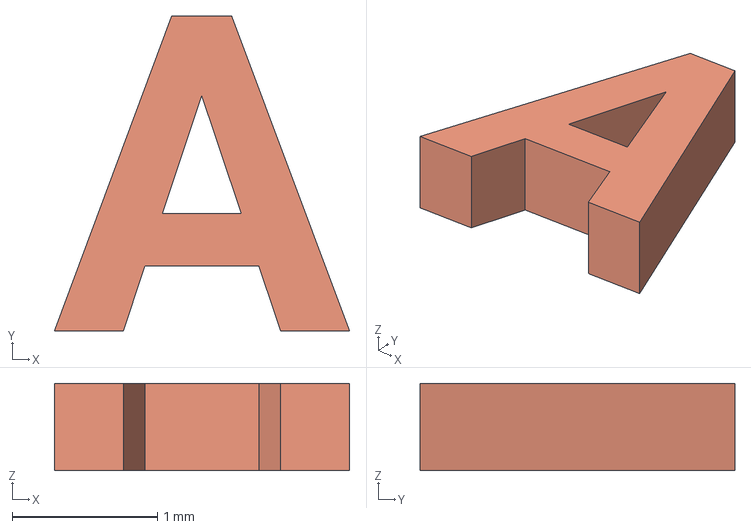
[picture p99: CAD file, 2025-08-02]
Sources/Case/Keycap STEP/zx81-keycaps-text-b-83.step
2.03 x 2.17 x 0.6 mm
