jgratton72/Purple-38er/Sources/Case/Keycap STEP/zx81-keycaps-text-a-46.step

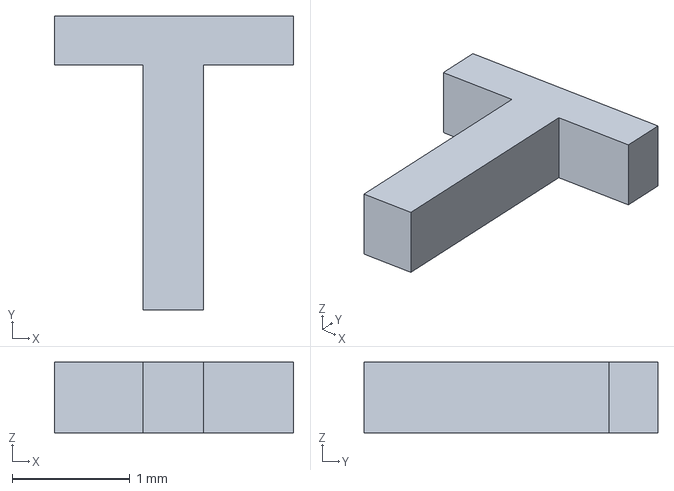
[picture p100: CAD file, 2025-08-02]
Sources/Case/Keycap STEP/zx81-keycaps-text-a-46.step
2.04 x 2.50 x 0.6 mm
