jgratton72/Purple-38er/Sources/Case/Keycap STEP/zx81-keycaps-text-b-66.step

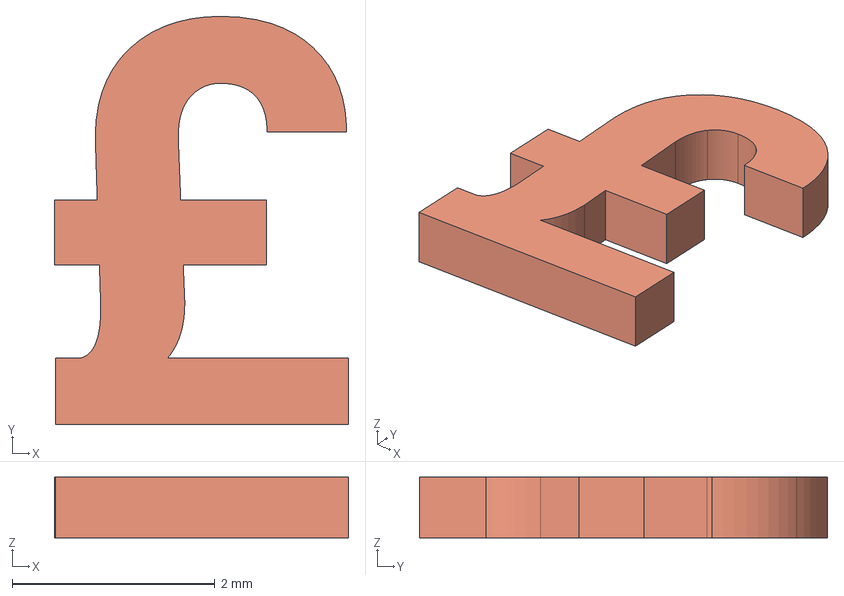
[picture p101: CAD file, 2025-08-02]
Sources/Case/Keycap STEP/zx81-keycaps-text-b-66.step
2.90 x 4.03 x 0.6 mm
