jgratton72/Purple-38er/Sources/Case/Keycap STEP/zx81-keycaps-text-b-85.step

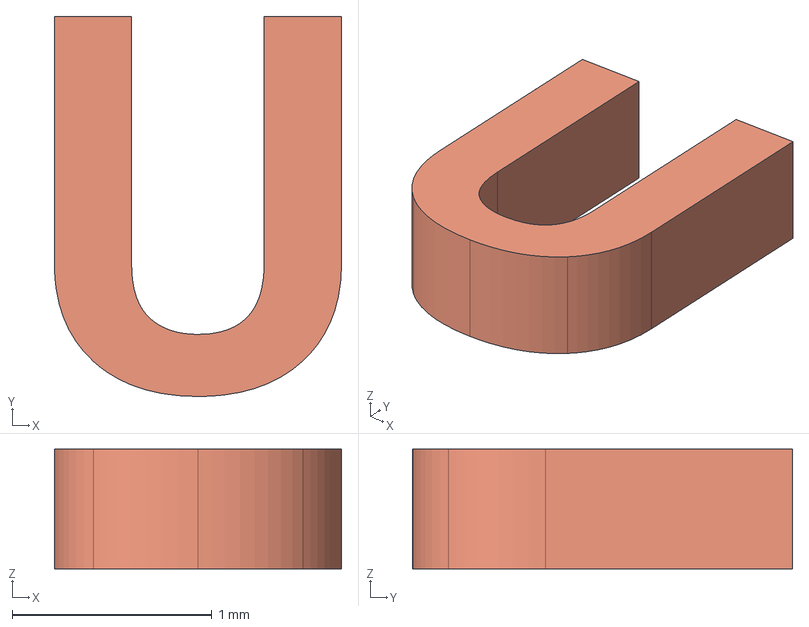
[picture p102: CAD file, 2025-08-02]
Sources/Case/Keycap STEP/zx81-keycaps-text-b-85.step
1.44 x 1.90 x 0.6 mm
