jgratton72/Purple-38er/Sources/Case/Keycap STEP/zx81-keycaps-text-a-25.step

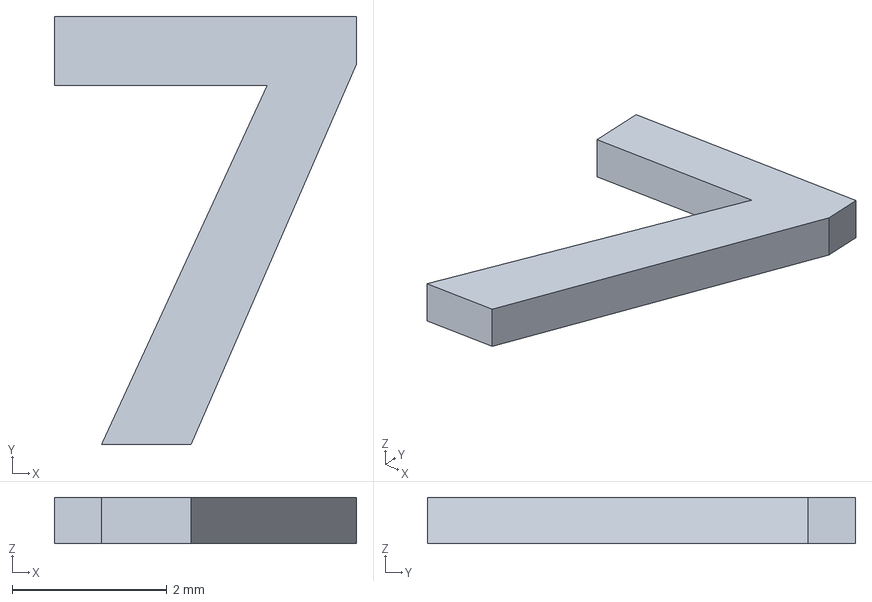
[picture p103: CAD file, 2025-08-02]
Sources/Case/Keycap STEP/zx81-keycaps-text-a-25.step
3.90 x 5.53 x 0.6 mm
