jgratton72/Purple-38er/Images/Assembly/IMG_1174.jpeg

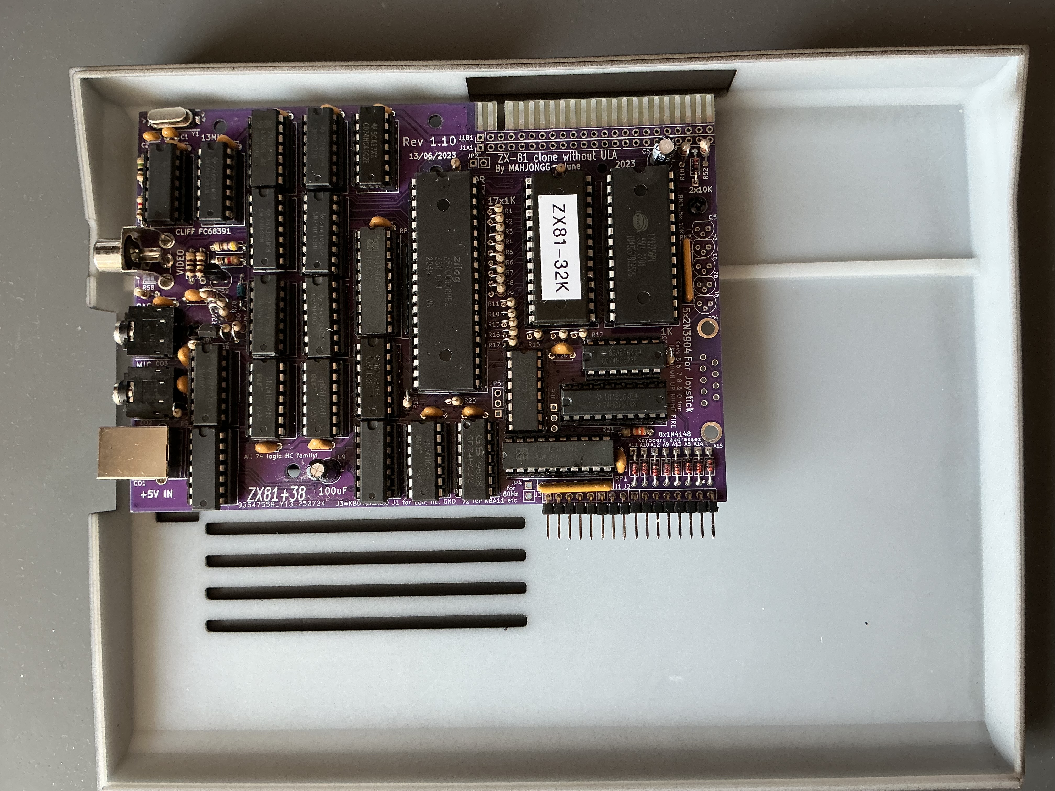
Images/Assembly/IMG_1174.jpeg
