jgratton72/Purple-38er/Images/Assembly/IMG_1176.jpeg

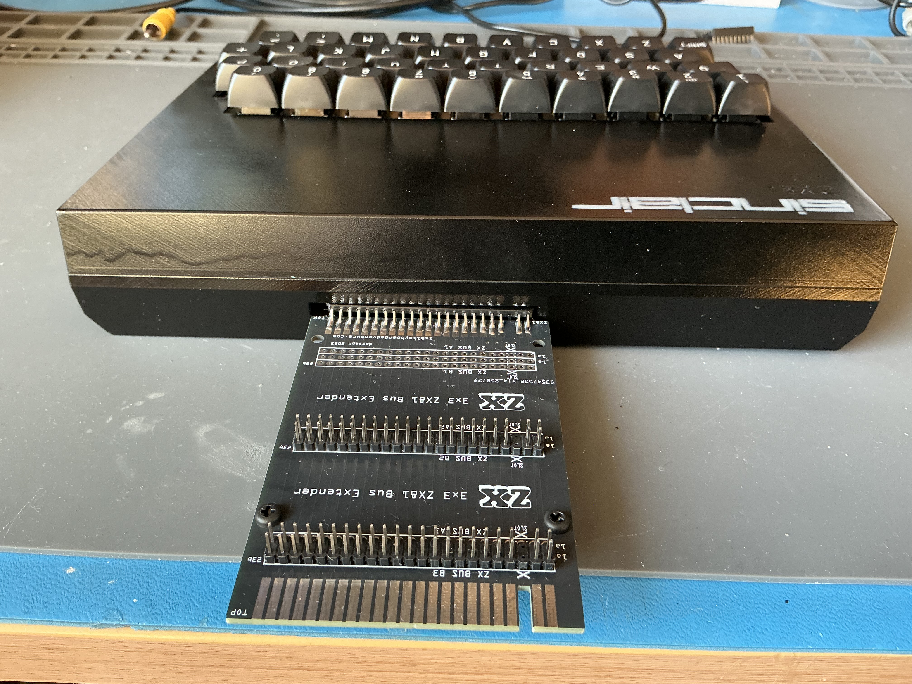
Images/Assembly/IMG_1176.jpeg
