jgratton72/Purple-38er/Images/Assembly/IMG_1177.jpeg

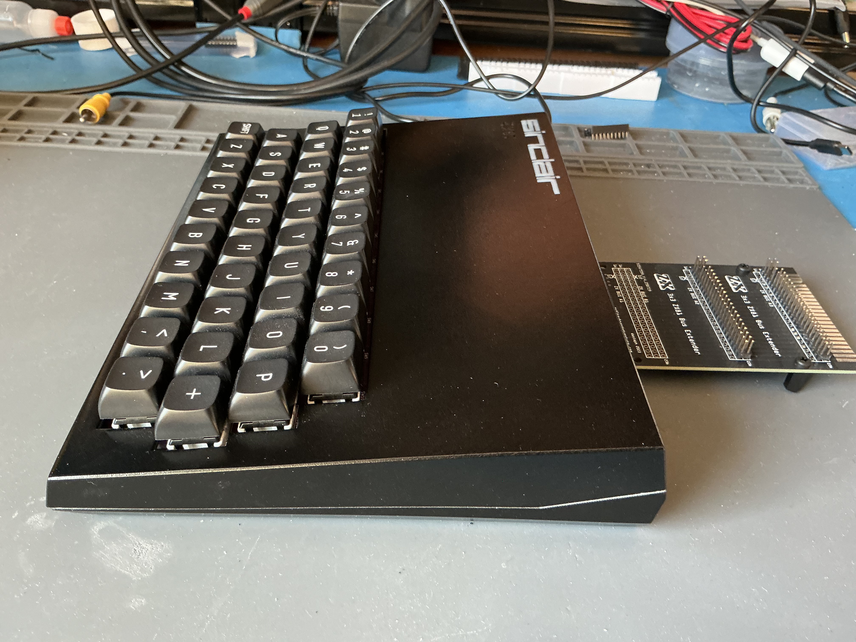
Images/Assembly/IMG_1177.jpeg
