jgratton72/Purple-38er/Images/Assembly/IMG_1178.jpeg

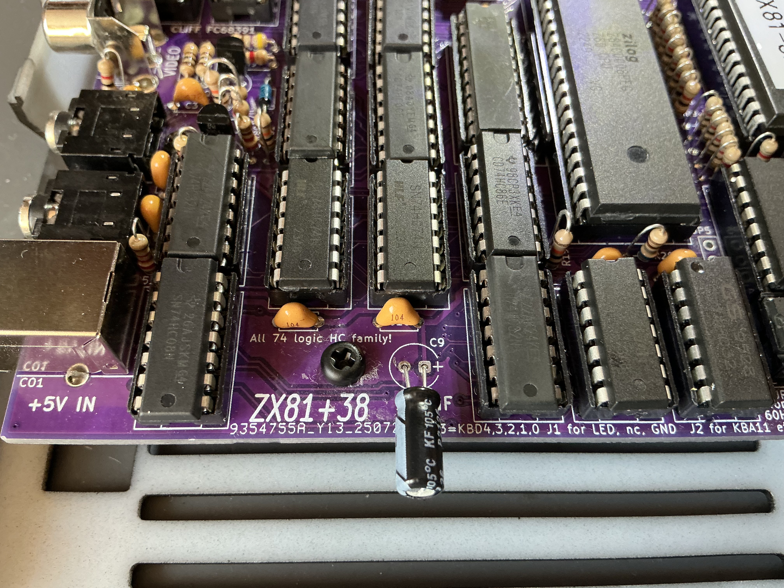
Images/Assembly/IMG_1178.jpeg
