jgratton72/Purple-38er/Images/Assembly/IMG_1179.jpeg

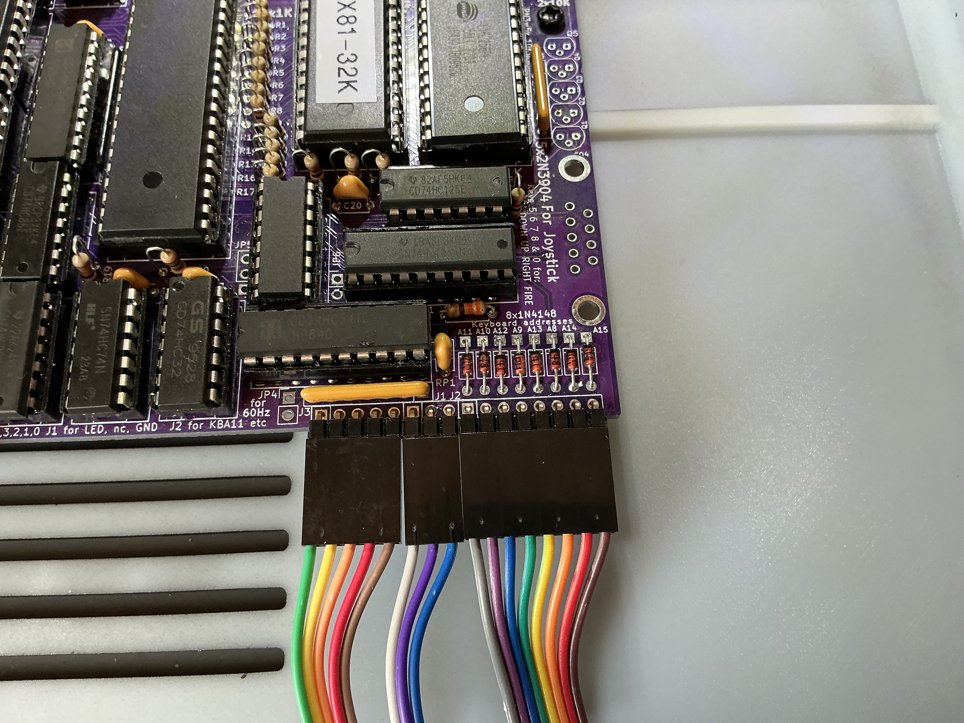
Images/Assembly/IMG_1179.jpeg
