jgratton72/Purple-38er/Images/Assembly/IMG_1180.jpeg

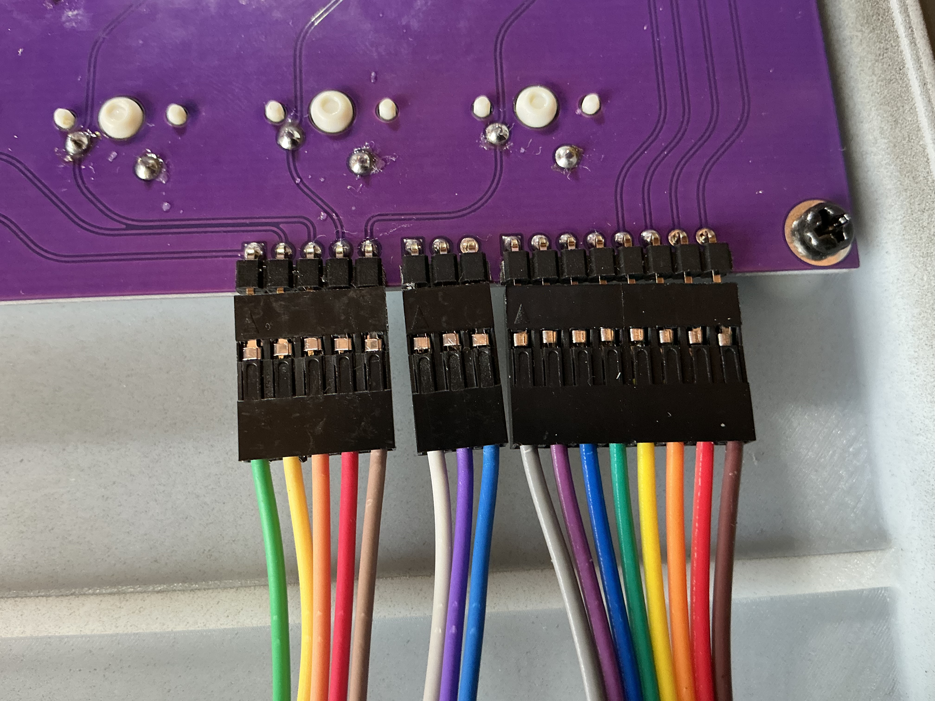
Images/Assembly/IMG_1180.jpeg
