jgratton72/Purple-38er/Images/Assembly/IMG_1182.jpeg

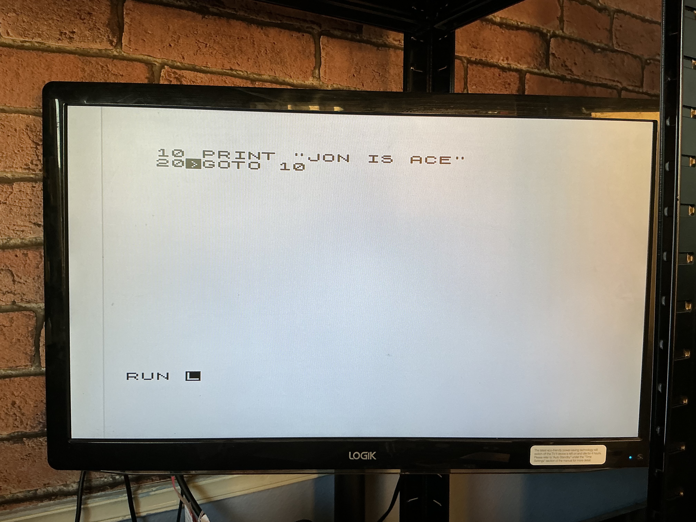
Images/Assembly/IMG_1182.jpeg
