jgratton72/Purple-38er/Images/Assembly/IMG_1183.jpeg

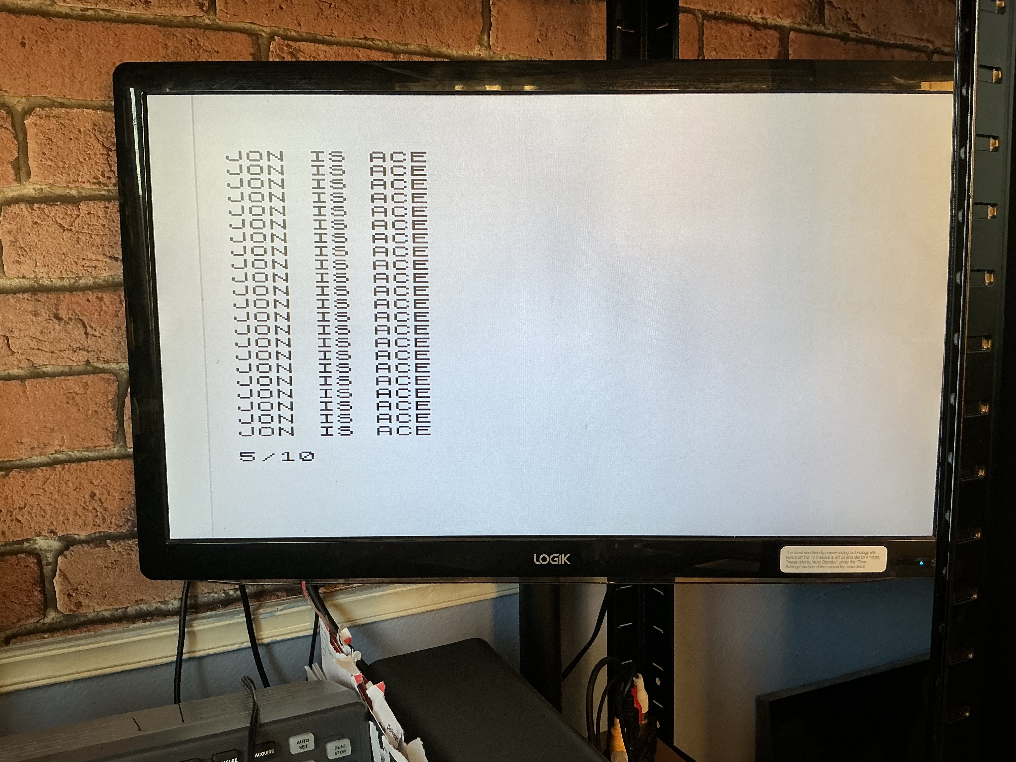
Images/Assembly/IMG_1183.jpeg
